nethunter/bleep/docs/scenes.md

# Scenes

## Purpose

A scene coordinates devices and groups through a non-blocking, ordered
sequence. It must remain transport- and brand-independent.

First panel scenario — Press Record (Start):

1. start recording on the Canon camera;
2. wait 500 ms;
3. start recording on the Tascam recorder.

Press Stop (generated by reversing and inverting Start):

1. stop recording on the Tascam recorder;
2. wait 500 ms;
3. stop recording on the Canon camera.

Later example with lights/groups (full Phase 6 gate):

1. turn on the light group;
2. wait one second;
3. start recording on the camera;
4. wait one second;
5. start recording on the Tascam recorder.

The panel and Portal generate a materialized reverse/inverse Stop by default
(ADR-037). The user can copy that preview into a separately authored Custom
Stop, preserving the flexibility introduced by ADR-019. Every target is
prepared concurrently when the sequence run screen opens, with links held
until Back or Unlink (ADR-020). ADR-021 supplies one scanner and independent
async connection slots, so selecting one target does not stop discovery for
the other preparing targets. A physical BLE connection alone is insufficient:
the runner remains `Connecting` until every driver also publishes protocol
readiness after its required discovery, subscriptions, and initialization.
Connection preparation may overlap, but actions and waits execute exactly in
their authored order; the seeded 500 ms wait is editable scene data, not an
engine-level recording delay.

Add Sequence uses a bounded three-stage authoring flow on both panel and Portal:
add and order Start steps, advance to the generated Stop preview, optionally
customize that materialized list, then name and Finish the sequence. The panel
reuses the standard Rename keypad for the final Name. For power-capable lights,
the compound light action applies one stored CCT or RGB look and then powers on
the same fixture without releasing pending state between stages. Its generated
inverse is one Turn Off. Aputure and Zhiyun lights expose this compound action;
Home Assistant lights retain their capability-safe power action.
Existing sequences retain direct Start and Stop editors. Older development
two-step light sequences are unsupported on the selected clean-storage
baseline.

Sequence Settings includes **Duplicate** alongside Rename and the Start/Stop
editors. A duplicated sequence preserves the enabled state, Start steps, Stop
mode, and materialized Stop steps, receives a new stable ID, and opens as
`Old Name (2)`. Names at the 31-character storage limit are shortened before
the suffix so `(2)` remains visible. The Portal suggests the same name while
still allowing it to be changed before duplication. The panel action list
scrolls vertically so Duplicate and Delete remain fully reachable.

Each existing Start or Custom Stop row opens a prefilled step editor. Generated
Stop is read-only until **Customize Stop** copies it into Custom mode. **Use
generated Stop** confirms before discarding the override and relinking Stop to
Start. Wait rows expose a
bounded millisecond duration control, parameterized **Set look** or
**Set look + On** rows
preserve and edit their saved CCT/RGB values, and ordinary action rows reopen the target's
capability-safe action picker. Saving replaces that row in place rather than
appending another step. Back from this existing-step editor returns directly to
the step list; changing target or action is done by adding a replacement step
and reordering it. Taller two-tier rows keep the action label above the
reorder/delete buttons. `Add step` is the final scrollable row rather than fixed
screen chrome, and adding a Wait uses the same duration editor.
New Wait steps default to 200 ms; existing saved waits retain their authored
duration.

Editing a prepared scene reconciles its target set in place. Links for targets
that remain in the materialized Start/Stop lists stay held, removed targets are
released, and newly added targets prepare before the scene returns to `Ready`.
Completing Stop keeps prepared links while the run/edit screen remains open so
the sequence can be edited or restarted without reconnecting. Back and Unlink
perform teardown.

Deleting a sequence while it is only preparing connections first cancels that
preparation and releases its links, then removes the record. Delete remains
disabled while Start/Stop is executing or the sequence is armed.

The run screen deduplicates direct targets across both authored lists and shows
each as a circular category-icon chip. The border communicates live readiness:
breathing cyan while connecting or initializing, green when protocol-ready,
red after a terminal connection failure, and muted gray when simply
disconnected or powered off. Retry backoff remains part of Connecting and keeps
breathing cyan. Tapping a chip outside Start/Stop execution opens that target's
full controls using the held activation. Returning preserves all links and the
sequence's logical phase; manual record commands are per-device overrides, so a
later authored Stop still runs for every target. Sequence Start/Stop controls
stay disabled while any stable-phase target is not ready.
The compact run status uses blue for connection/transitions, green for
Ready/Done, red for Recording/failure/disconnection, and muted text for Idle.

A partial Start action failure keeps sequence ownership and exposes Stop.
Generated and Custom Stop still visit every materialized target. Canon Smart and Tascam
treat Stop as a successful no-op when that device already confirms `Stopped`,
so a target that never began recording cannot abort cleanup before another
target is stopped. Unknown or recording targets still receive the protocol Stop
command and require their normal device-originated confirmation. A successful
Stop reaches `Completed`, where Start is enabled for another attempt.

While a sequence run screen is open, a short hardware-button press mirrors the
enabled run action: Start when the sequence is ready (or restartable), and Stop
when it is armed or Start is in flight. It does nothing while preparation or
Stop is already in progress. A long press mirrors the visible Back control:
Settings closes first, the step editor returns to Run, Run returns to the
sequence list and releases sequence ownership, and the list returns Home.

## Data model

A scene contains:

- stable ID, name, enabled state, and schema version;
- ordered Start steps;
- Stop mode: generated inverse or Custom override, plus the materialized Stop
  list used by the current runner;
- default timeout and failure policy;
- optional descriptive notes.

The number of scenes is not a compile-time product limit. The registry grows
on demand. Schema-v4 persistence retains schema v3's compact authored-step
encoding and adds generated/custom Stop mode. Creation is transactional: if RAM
or NVS cannot hold another scene, that attempted scene is not committed and
existing scenes remain intact. The per-scene step bound is retained because the
runner and editor operate on fixed, explicitly validated Start and Stop command
lists.

Step types:

- `Action`: send one typed command to a device or group;
- `Wait`: schedule the next step after a duration;
- `Parallel`: execute a bounded list of child actions together.

An action stores a stable target ID and capability command, not a brand-specific
function name.

Conceptual example:

```json
{
  "id": "studio-record",
  "name": "Studio Record",
  "stopMode": "generated",
  "start": [
    {
      "type": "action",
      "target": "group:lights",
      "command": "light.power_on"
    },
    {
      "type": "wait",
      "milliseconds": 1000
    },
    {
      "type": "action",
      "target": "device:main-camera",
      "command": "recorder.start"
    },
    {
      "type": "wait",
      "milliseconds": 1000
    },
    {
      "type": "action",
      "target": "device:tascam",
      "command": "recorder.start"
    }
  ]
}
```

The final schema may use a compact binary representation in firmware, but the
Portal-mode HTTP API should expose a versioned, readable format.

## Authoring-time generation

Generated Stop walks Start backward and maps commands as follows:

- light on ↔ light off;
- recording start ↔ recording stop;
- record trigger, Home Assistant Press, and Activate repeat unchanged;
- absolute CCT/RGB settings are omitted because the previous value is unknown.

A wait reverses to the same duration. Generated Stop is refreshed atomically
after every Start add, edit, reorder, or delete. Custom Stop is independent and
is not modified by later Start edits.

Schema 4 stores the mode and materialized list. Version 0.3.0 accepts only that
current encoding; older development schemas are rejected at load and are not
migrated or erased automatically.

## Execution journal

Success journaling remains later Phase 6 work. The current generated Stop is
authoring-time data and intentionally preserves the existing cleanup rule:
after partial Start failure, Stop attempts every generated target because a
device may have acted without confirming success.

Journal state includes:

- scene and run IDs;
- current step and direction;
- started, completed, failed, skipped, and canceled results;
- per-device group results;
- timestamps and state quality.

Persistence across power loss is a later policy decision. The initial engine
must fail safe and show that the previous run ended unexpectedly.

## Timing and concurrency

`Wait` is scheduled from monotonic time. It must not call `delay()` or block
Bluetooth, HTTP, LVGL, reconnect, or cancellation.

Parallel execution is bounded by configured queue and connection limits.
“Parallel” means dispatched without an intentional ordering delay, not
electrically or transactionally simultaneous.

## Failure policies

Each step may use:

- `abort`: stop Start execution and expose completed actions for rollback;
- `continue`: record failure and proceed;
- `retry`: retry within a bounded count and timeout.

No scene is atomic across independent hardware. UI and HTTP responses must show
per-step and per-device results.

## Validation

Before saving or running, validate:

- target IDs exist and are enabled;
- target drivers are compiled into this firmware;
- device or group exposes the command capability;
- generated Stop follows the ADR-037 command mapping;
- waits, retries, and timeouts are within configured limits;
- queue and nesting limits are respected;
- movement actions satisfy additional safety rules.

## Portal-mode HTTP editing

The temporary Portal-mode access point provides:

- scene list, create, duplicate, rename, enable/disable, and delete;
- ordered drag/reorder editing;
- device/group target picker filtered by capability;
- action parameters and wait duration;
- generated Stop preview;
- optional explicit Stop editor;
- validation results;
- import/export and a dry-run validation endpoint.

Editing APIs exist only while Portal mode is active. Exiting Portal mode or
reaching its inactivity timeout stops the HTTP server and access point.
