nethunter/bleep/docs/decisions.md

# Architecture Decisions

This log records accepted decisions. Add a new numbered entry when a choice
changes architecture, compatibility, persistence, safety, or user workflow.
Do not silently rewrite an accepted decision; mark it superseded and reference
the replacement.

## ADR-001: Direct on-device control

- Status: Accepted
- Decision: Device integrations and scene execution run on the ESP32-C3 remote,
  not on an external gateway.
- Consequence: Bluetooth Mesh, GATT, Wi-Fi, HTTP, LVGL, and scene scheduling
  must coexist within a constrained memory budget.

## ADR-002: Compile-time driver selection

- Status: Accepted
- Decision: Use ESP-IDF Kconfig/menuconfig to choose device families, model
  drivers, transports, and optional subsystems.
- Consequence: Disabled drivers must be removed from the binary. Runtime
  enable/disable controls behavior but does not reclaim linked memory.

## ADR-003: Drivers and instances are separate

- Status: Accepted
- Decision: Compiled drivers describe supported models; persistent runtime
  instances contain pairing, endpoint, name, enabled state, and group data.
- Consequence: One driver can support multiple physical devices, and dormant
  instance records survive a build that omits their driver.

## ADR-004: Unified capability UI

- Status: Accepted
- Decision: Reuse UI modules by device type and capability rather than by
  brand. Drivers may add specialized extensions where necessary.
- Consequence: Lights, cameras, motion devices, and recorders receive
  consistent controls while Shark retains its specialized keypoint workflow.

## ADR-005: Amaran onboarding supports two paths

- Status: Accepted
- Decision: Support both panel-owned provisioning of factory-reset lights and
  import of an existing Sidus/amaran mesh.
- Consequence: The first release uses one active studio mesh and treats mesh
  keys as secrets.

## ADR-006: Canon supports Bluetooth and HTTP

- Status: Accepted
- Decision: Canon EOS R6 family drivers support BR-E1-compatible Bluetooth and
  CCAPI HTTP independently, including HTTP with Bluetooth fallback.
- Consequence: HTTP can provide confirmed recording state; Bluetooth-only state
  is optimistic unless later protocol research finds reliable readback.

## ADR-007: Groups are capability-safe

- Status: Accepted
- Decision: A group exposes only capabilities shared by all enabled members.
- Consequence: Commands and scene steps cannot silently target unsupported
  members.

## ADR-008: Scenes are ordered and reversible

- Status: Accepted
- Decision: Scenes contain ordered actions, waits, and optional parallel
  groups. Stop is generated by reversing/inverting successful Start actions by
  default, with an explicit Stop override available.
- Consequence: Commands declare safe inverses and execution uses a per-action
  journal.

## ADR-009: Administration is USB-only

- Status: Superseded by ADR-011
- Decision: Serve the HTTP administration portal on PPP or SLIP over USB
  serial, never on Wi-Fi.
- Consequence: Wi-Fi remains available for outbound Canon CCAPI, while portal
  availability depends on the USB network link. Host setup and upload/logging
  coexistence require an early feasibility spike.

## ADR-010: Main-loop ownership

- Status: Accepted
- Decision: All parsing, state mutation, commands, scene transitions, and LVGL
  access occur from `loop()`. Transport callbacks only queue bytes or events.
- Consequence: New transports must be bounded and non-blocking.

## ADR-011: Administration uses a dedicated temporary AP mode

- Status: Accepted
- Decision: The administration HTTP server runs only in an explicit Portal
  mode on a temporary open SoftAP or its bounded station handoff.
- Consequence: Entering Portal mode suspends scenes, device links, and studio
  Wi-Fi. Exit, inactivity timeout, or reboot destroys the HTTP server and AP.
  No administration listener consumes resources during normal operation.

## ADR-012: Boot always opens Home

- Status: Accepted
- Decision: Startup displays a neutral Home menu and does not automatically
  scan, pair, re-pair, reconnect Shark, or load a device screen.
- Consequence: Opening a device screen or launching a scene explicitly requests
  the required connections. Devices, Groups, Scenes, Portal, and power/status
  are available from Home.

## ADR-013: Advance the multi-device foundation before feasibility spikes

- Status: Accepted
- Decision: Implement the bounded driver catalog, device manager, persistent
  runtime registry, Home/Devices UI, and on-demand Shark lifecycle before the
  Phase 1 coexistence and Portal spikes. The first build compiles only the Shark
  driver and permits one Shark instance, while retaining up to eight dormant or
  future device records.
- Consequence: This is an explicit roadmap deviation that advances selected
  Phase 2, Phase 3, and Phase 7 work while the Phase 0 physical behavior gate
  and Phase 1 feasibility gates remain open. No Amaran, Canon, group, scene, or
  Portal support is implied by the framework.
- Persistence: Registry schema version 1 is stored as a checked NVS blob in the
  `studio` namespace. Existing `shark` pairing keys migrate into the initial
  record and remain available for rollback until hardware verification passes.
- Lifecycle: Boot loads configuration and Home without initializing NimBLE.
  Opening the enabled Shark record activates scan/connect/reconnect; leaving its
  screens stops motion, scanning, retries, and the connection.

## ADR-014: Canon BLE exposes an honest record trigger

- Status: Accepted
- Decision: Advance a bounded Canon BR-E1 BLE tranche for EOS R6 Mark III
  hardware research before the full Phase 1 coexistence gate. The BLE
  capability is a stateless record trigger, not separate record-start and
  record-stop commands.
- Consequence: The panel does not infer or display recording state from BLE.
  BR-E1 sends the same movie trigger for both transitions and provides no
  equivalent state readback. Distinct start/stop commands and confirmed state
  remain CCAPI work. The tranche may use the existing one-active-instance
  manager and does not prove concurrent Shark/Canon links or complete Phase 1.
- Protocol status: Pairing, bonded reconnect, and the movie-mode `0x88`/`0x08`
  press/release sequence from public reverse-engineering are functionally
  verified on the EOS R6 Mark III. Captures and extended stability measurements
  remain `Research`.

## ADR-015: Canon exposes Trigger and Smart drivers

- Status: Accepted
- Decision: Present the two Canon workflows as separate compiled drivers and
  device choices: `Canon (Trigger)` for BR-E1-compatible BLE, and
  `Canon (Smart)` for smartphone-mode BLE handoff followed by direct Wi-Fi
  CCAPI.
- Consequence: Trigger remains the fast stateless fallback. Smart owns
  smartphone-mode pairing, requests the camera Wi-Fi access point, obtains the
  handoff connection data, joins that network, and uses CCAPI for distinct
  record start/stop and confirmed state. A Smart failure may fall back to a
  separately configured Trigger instance only when the user selects that
  policy.
- Research status: Sanitized EOS R6 Mark III host-HCI fixtures identify the
  Camera Connect request that starts Wi-Fi, its response indications, and the
  SSID-like and credential-like characteristics. `Canon (Smart)` remains
  blocked until network-side capture identifies security mode, DHCP behavior,
  the camera HTTP endpoint, and the first successful CCAPI request. Do not infer
  those missing details from successful BLE handoff alone.

## ADR-016: Tascam X8 record-control tranche

- Status: Accepted
- Decision: Advance the Tascam Portacapture X8 from the future recorder list as
  a bounded AK-BT1 BLE tranche with connect, explicit record start, explicit
  record stop, and recorder-confirmed recording state.
- Evidence: The annotated nRF52840 research capture summarized in
  `docs/protocols/tascam-x8.md` confirms the custom GATT service, COBS stream
  envelope, session keepalive, start/stop commands, and state events for both
  app-originated and recorder-originated actions. Golden vectors and confidence
  labels are recorded in `docs/protocols/tascam-x8.md`.
- Consequence: Tascam gets typed `RecordStart` and `RecordStop` commands rather
  than reusing Canon Trigger's stateless toggle. The UI may show recording only
  after the recorder's confirmed `DR 20 20 24 01` start event and stopped only
  after `DR 10 20 08`; ATT write responses are not physical success. No stable
  recording boolean was confirmed in the original fixture. A subsequent
  controlled reconnect capture confirms `DR 20 20 00` values `0x81` recording,
  `0x10` stopped, and transitional `0x82`. Battery, media status, mixer control,
  and other Portacapture functions remain future research.
- Roadmap deviation: This tranche advances a future recorder driver while the
  Phase 0/foundation and Canon verification gates remain open. It does not
  begin dependent scene or group work and retains one active transport.

## ADR-017: Canon smartphone BLE ships beside Trigger

- Status: Experimental
- Decision: Compile both ADR-015 Canon choices. `Canon (Trigger)`
  (`DriverId::CanonTrigger = 4`) keeps the verified BR-E1 remote service
  (`00050000-...`, movie-mode `0x88`/`0x08`). `Canon (Smart)`
  (`DriverId::CanonBle = 2`) keeps the Camera Connect smartphone-mode BLE
  pairing and shooting services as a BLE-only experiment until CCAPI handoff
  evidence lands. Both may be present in one firmware build; the operator
  picks the matching camera menu (Remote vs Connect to smartphone). Only one
  transport remains active at a time.
- Evidence: Public EOS M6 Camera Connect reverse-engineering documents the
  `00010000-...` handshake service and `00030000-...` shooting service. The
  minimized EOS R6 Mark III host-HCI research findings summarized in
  `docs/protocols/canon-smartphone-ble.md` confirm confirmation-first pairing,
  explicit movie start/stop writes,
  shooting-state notifications, and the `00020002-...` Wi-Fi handoff request
  with `00020003-...` responses. The handoff fixture excludes serial,
  controller, SSID-like, credential-like, and SMP key material. BR-E1 Trigger
  remains hardware-verified on EOS R6 Mark II/III.
- Consequence: Smart exposes explicit `RecordStart`, `RecordStop`, and
  recording-state capability, but reports state as unknown until a
  camera-originated `00030031-...` notification is observed. ATT write success
  is not recording confirmation. Trigger stays stateless (`RecordTrigger` only).
  Existing BR-E1 bonds and Smartphone bonds are not interchangeable; forget and
  re-pair when switching modes or bodies.
- Relationship to ADR-015: Smart remains a bounded BLE-only experiment, not the
  production BLE-to-Wi-Fi CCAPI workflow. It does not start a camera access
  point, join Wi-Fi, or implement CCAPI.
- Research boundary: Camera Connect's BLE handoff is captured, but the camera
  network's DHCP/endpoint details and first successful CCAPI request are not.
  Full `Canon (Smart)` Wi-Fi/CCAPI remains blocked on that network-side evidence.
- Roadmap deviation: This experiment advances smartphone-mode pairing and
  BLE-only record control while the Phase 0/foundation and Canon Smart handoff
  gates remain open. It retains one active transport and does not begin scene
  or group work.

## ADR-018: Canon BLE power is explicit and non-destructive

- Status: Experimental
- Decision: Opening the Canon smartphone screen automatically sends captured
  wake mode `03` after setup. Camera power-down is available only through an
  explicit on-screen power control using mode `05`. After confirmed power-down,
  the same control reconnects and runs the captured wake sequence. Reacquiring
  the retained powered-off session from a device screen or sequence also starts
  that reconnect-and-wake attempt; Back only releases the panel's BLE
  connection.
- Safety: Power-down is unavailable while recording is camera-confirmed or a
  record command is pending. Result `01` is only protocol acknowledgement; the
  expected camera-side disconnect is required before the panel reports
  `Powered off`.
- Evidence: The sanitized host-HCI handoff fixture contains repeated
  `03`/`05` wake sequences and `05`/`01` power-down followed by camera-side
  disconnects approximately 147-154 ms later.
- Consequence: A failed or missing power-down disconnect leaves the session
  connected and reports failure instead of assuming physical success. The
  workflow remains hardware-unverified until the ADR-017 gate is exercised.

## ADR-019: Scenes use authored Start and Stop sequences

- Status: Superseded by ADR-037
- Decision: The first on-device scene tranche stores and runs separate ordered
  Start and Stop step lists. Generated reverse-Stop from ADR-008 remains a
  later option, not the default for panel-authored sequences.
- Consequence: Press Record and Press Stop may differ in order, waits, and
  targets. Validation requires at least one non-empty list and capability-safe
  action targets. No inverse journal is required for Stop generation in this
  tranche; per-step progress is still tracked for the UI. Authored Stop remains
  available after a partial Start failure. A Stop action against a target that
  already confirms `Stopped` succeeds as an idempotent no-op, allowing cleanup
  to reach later targets and a completed Stop to make Start retryable.
- First scenario: Start sends Canon `RecordStart`, waits 500 ms, then Tascam
  `RecordStart`. Stop sends Canon `RecordStop`, then Tascam `RecordStop`.

## ADR-020: Sequence runs hold concurrent device links

- Status: Accepted (amended 2026-08-04, 2026-08-09, and 2026-09-03)
- Decision: Opening a sequence run screen prepares every distinct Start/Stop
  target concurrently (`Connecting` → `Ready`). `Ready` requires both a
  physical link and driver-confirmed protocol readiness after required
  discovery/subscriptions/initialization. Links stay held while the run
  screen is open, during Start/Stop execution, while armed after Start, and
  after a successful Stop for immediate restart. Opening Settings, leaving the
  run screen (Back/hide), or selecting Done releases sequence ownership and
  cancels pending preparation so configuration remains editable. Manual
  device screens retain exclusive single-active activation outside sequence
  holds. A sequence target chip may temporarily open that target's full device
  screen by borrowing its held activation; Back returns to the sequence without
  releasing any held target.
- Transition ownership: Switching directly between sequences transfers the
  intersection of their target sets without an ownerless gap. A target shared
  by both sequences, and any physical transport group backing that target,
  remains protected from eviction. Old-only targets are released first and
  become the preferred safe reclamation candidates before new-only targets are
  acquired. This applies equally to retained HA/Wi-Fi and BLE transports.
- Consequence: `DeviceManager` supports a bounded multi-active set across
  different compiled drivers (Canon Smart + Tascam in the first tranche). Start
  from `Ready` does not re-activate targets. Prepare/connect failures surface
  on the run screen. Device screens opened outside the sequence remain blocked
  while it holds links. Sequence-owned target controls are disabled during
  Start/Stop execution, and Start/Stop remain unavailable while any target is
  not protocol-ready. A physical target that reports `pairingRejected` (the
  peer accepts the link and terminates it before bonding, repeatedly) fails
  preparation immediately with `Re-pair <device>` rather than consuming the
  connect budget; the operator must re-pair before the sequence can run. Physical targets are acquired recorders first, then lights, then
  cameras (2026-09-04): the shared central runs one connect at a time, a
  recorder establishes in under a second when awake, and a sleeping camera
  holds the procedure through several failed pokes. Step execution keeps the
  authored order.
  Settings never cancels an active Start, armed recording,
  Stop, or action failure that still permits authored Stop cleanup. A short
  hardware-button press invokes the enabled
  Start/Stop action; a long press follows the same Back path as touch and never
  dispatches Start or Stop. Shark motion remains outside sequences.
- Roadmap deviation: This advances a bounded Phase 6/7 panel-scene tranche
  ahead of groups, Portal HTTP editing, lights, and generated reverse-Stop.

## ADR-021: One shared BLE central owns transport mechanics

- Status: Accepted
- Decision: One lazily initialized BLE central runtime owns NimBLE
  initialization, the physical scanner, bounded client slots, asynchronous
  connect/disconnect callback routing, reconnect timing, address claims,
  controller bond operations, and teardown. Device clients keep advertisement
  acceptance, pairing policy, GATT discovery/subscription, protocol
  handshakes, commands, and notification parsing.
- Threading: NimBLE callbacks copy fixed-size scan, link, and security events
  into a bounded queue. The central and device clients consume those events
  from the Arduino main loop; callbacks do not mutate device state, perform
  GATT writes, or access LVGL.
- Lifetime: Home boot remains BLE-free. The runtime initializes on the first
  acquired link and shuts down after the last owner releases it. Because
  NimBLE client deletion completes asynchronously, shutdown continues pumping
  teardown until the global client slots are actually free. An immediate
  reacquire may reserve logical links while those clients retire; replacement
  clients are provisioned without failing scene activation, and callbacks from
  retired client pointers are ignored. `DeviceRecord` remains the persistent
  identity source; controller bonds are transport state, not a second pairing
  registry.
- Consequence: Concurrent sequence preparation shares one scanner and separate
  async connection slots. Physical connection initiation and security
  procedures are controller-serialized after hardware produced repeated HCI
  `0x3e` establishment timeouts under simultaneous attempts. Discovery remains
  shared, and a queued target may connect while an established target performs
  protocol initialization. Protocol-specific candidate dwell, ignored-peer,
  and direct-versus-scan policy remains in each client. Clients may also cap
  the growing direct-retry backoff (`ConnectPolicy::retryBackoffCapMs`) when
  their peripheral's post-failure silence is a fixed interval; Canon Smart
  uses 1.5 s. `connectPriority` orders queued connects (recorders ahead of
  cameras), `directAttemptsBeforeScan = 0` selects listen-first for peers
  whose blind poke is costly, advertisements carry a `connectable` flag and
  non-connectable ones never start a connect, and the shared scan runs
  without duty-cycle pauses for 15 s while a saved peer that just failed to
  establish is sought (measured AK-BT1 silence after a failed poke: 6-30 s).
- Measurement boundary (2026-08-04): targeted discovery, next-loop setup,
  readiness telemetry, and best-effort connection parameters are implemented
  without changing ownership. A shared asynchronous GATT executor is deferred
  unless hardware timing shows blocking GATT work is at least 25% of median
  readiness for a driver or the Canon Smart + Tascam sequence pair. If that
  gate triggers, amend this ADR before moving generic GATT mechanics into the
  shared layer; drivers retain UUID profiles and protocol semantics.

## ADR-022: Protocol-ready device links persist in a bounded pool

- Status: Accepted
- Decision: `DeviceManager` keeps up to `CONFIG_MAX_ACTIVE_INSTANCES` logical
  sessions active after their screen or sequence owner leaves and maps them
  onto at most `CONFIG_MAX_ACTIVE_LINKS` physical BLE transport groups. A
  driver's `BleSlotKey` is per-instance by default, empty for a non-BLE runtime,
  or shared by logical instances that demonstrably use one real connection.
  Boot remains BLE-free, and an attempt that has never reached protocol
  readiness is canceled when its last owner leaves.
- Ownership: Foreground device screens and sequences hold independent owners.
  Reopening or preparing an already-active instance reuses its session. Leaving
  removes only that owner; retained sessions continue bounded reconnect after
  an unexpected drop. Canon's explicit power-down remains intentional and does
  not trigger reconnect until requested.
- Capacity and safety: When four distinct BLE keys are active, acquisition of
  a fifth key evicts the least-recently-used retained transport group only when
  every logical member has no owner, pending command, or confirmed recording.
  All members are deactivated together so the shared central link is actually
  released. Acquiring another member of an existing group consumes no new
  physical slot. If no group is safe, acquisition fails. Confirmed-recording
  links require explicit confirmation before manual Disconnect. Disconnect,
  disable, forget, remove, Portal entry, and controller shutdown release the
  session without treating an ACK as proof of device state.
- Scene handoff: changing scenes transfers ownership for targets in the set
  intersection and releases ownership for old-only targets. Release does not
  disconnect protocol-ready sessions. No scene-specific cleanup bypasses the
  pool: ownerless Canon, Tascam, HA, and light sessions remain retained while
  logical and BLE capacity permit, and only a subsequent capacity-driven LRU
  acquisition may evict them.
- Supersedes: This replaces ADR-013's leave-screen teardown, ADR-018's statement
  that Back releases the Canon link, and ADR-020's leave-sequence teardown and
  manual single-active restriction. Their boot, power safety, sequence
  readiness, and borrowed-control decisions remain accepted.
- Consequence: The shared BLE runtime remains initialized while any retained
  transport group owns a central slot. Under ADR-030 the panel-owned
  Amaran/Aputure/Zhiyun mesh has one shared key; Home Assistant has none.
  Static per-driver session storage must remain within measured ESP32-C3 RAM.

## ADR-023: Bounded local Home Assistant entity client

- Status: Experimental; amended 2026-08-04; hardware feasibility gate open
- Decision: Add one shared Home Assistant client for at most four selected
  `light`, `switch`, `input_boolean`, `button`, `scene`, and `script` entities.
  V1 is client-only: Ble(e)p does not expose its physical devices to Home
  Assistant. Lights are power-only. Local plaintext `http://` and `ws://`
  endpoints plus a pasted long-lived access token are allowed; TLS, cloud
  access, OAuth, devices/areas, and other domains remain deferred.
- Provisioning boundary: First-time Portal setup performs a bounded nearby-network
  scan before creating an open SoftAP. The AP console administers local device
  records and sequences without studio Wi-Fi and may collect studio Wi-Fi
  credentials for Home Assistant. The initial scan is cached, but an explicit
  browser request starts a fresh non-blocking scan while preserving AP HTTP/DNS
  service. The panel exposes the setup AP as a standard
  open-network Wi-Fi QR code. Wildcard DNS and HTTP redirects trigger the phone's
  captive-network sign-on UI on a best-effort basis while that AP is active;
  both are destroyed before LAN Portal startup. Manual SSID entry remains
  available for hidden networks. During the non-blocking join it uses AP+STA while the listener
  remains bound to SoftAP and both the browser and panel report progress or a
  bounded failure reason.
  After a successful join, it destroys the AP listener and AP, then binds a new
  listener to the station address. The assigned numeric address is authoritative
  and shown during handoff; `http://bleep.local` is a best-effort mDNS alias.
  The LAN Portal enables Home Assistant URL/token/entity setup and is reachable
  only while Portal remains open on the panel. Entering Portal cancels scenes
  and physical links; explicit Exit or ten minutes of inactivity destroys the
  listener and disconnects Wi-Fi. Normal Home boot remains network-free.
- Persistence and capacity: Device schema v2 adds a tagged HA domain and
  canonical entity ID while decoding v1 BLE records unchanged. Wi-Fi password
  and HA token live in a separate checksummed NVS record and are excluded from
  ordinary device backup/UI responses. The registry grows from eight to twelve
  records: eight physical records plus four HA entities. Active runtime-instance
  capacity is separate from the four-link BLE transport limit because HA
  instances share one network session.
- Runtime: Use Home Assistant's documented bearer-token REST API and
  authenticated `/api/websocket` API only. Resolve initial states individually,
  subscribe only to active entities with `subscribe_trigger`, and rebuild that
  subscription as ownership changes. WebSocket callbacks enqueue bounded raw
  frames; JSON parsing, state mutation, service calls, and LVGL access stay in
  `loop()`. A successful authenticated subscription is command-ready even when
  heap pressure defers initial REST state confirmation; that entity remains
  explicitly unknown until REST or an event confirms it. A successful service
  result completes both stateful and stateless actions because an idempotent
  call may produce no state-change event; API acceptance does not upgrade the
  entity's independently reported state quality.
- Safety and scenes: Generic `TurnOn`, `TurnOff`, `Press`, and `Activate`
  commands are capability-checked through each instance's dynamic profile.
  Lights and switches expose explicit On/Off controls. Input booleans retain
  explicit On/Off commands for safe scene authoring but present one
  context-sensitive action button on their entity screen. HA scenes/scripts
  expose only Activate. No Toggle or value action is inferred.
  Portal refuses to remove an entity referenced by a Ble(e)p scene and may
  rebind an existing instance ID so those references survive entity-ID changes.
- Feasibility gate: Before this moves beyond Experimental, verify on the target
  board AP-to-LAN handoff, LAN listener lifetime, REST discovery, authenticated WebSocket subscription,
  LVGL responsiveness, teardown, and heap recovery across ten Portal and ten
  runtime connect/disconnect cycles. Stop promotion and document the limiting
  resource if any gate fails. The uncommitted multi-instance `DeviceManager`
  work present when this tranche began is the authorized implementation
  baseline and must be preserved.
- Hardware constraint observed 2026-08-04: Opening an authored HA-first mixed
  sequence started Wi-Fi before the lazy BLE central. NimBLE then failed its
  contiguous `0x7800` allocation (`BLE_INIT: Malloc failed`) and asserted into
  an interrupt-watchdog reset. Preparation now acquires all physical targets
  before HA targets regardless of authored action order. Amendment
  2026-09-03: the ordering protects NimBLE's initialization allocation, not
  peripheral wake time, so the platform may supply an early-network policy
  (`SceneRunner::setEarlyNetworkPolicy`). `main.cpp` permits HA Wi-Fi once
  the BLE central holds a link and free heap is at least 56 KB with a 40 KB
  largest block; otherwise HA still waits for every physical target. An
  early-started HA keeps the full network connect budget measured from the
  later of its own start and the moment the physical targets became ready.
  Station joins reuse the last successful channel/BSSID within a boot
  (`wifi_station_cache`), and the HA runtime turns the radio off through a
  settled main-loop shutdown instead of an immediate `WIFI_OFF`. A subsequent live
  run proved that two BLE sessions left too little heap for the Wi-Fi driver's
  four required RX buffers. At that tranche the target used two 20-row DMA display strips,
  a 76 KiB LVGL pool, and two 2 KiB HA frame slots. The complete simulator flow
  passes at those bounds; a measured 72 KiB LVGL pool was rejected. WebSocket
  disconnects now reset protocol state and schedule a main-loop reconnect
  instead of leaving the runtime permanently unauthenticated. These
  mitigations have native/simulator coverage, and one mixed
  HA/Canon/Tascam hardware run reached all-targets-ready in 8.6 seconds. The
  ten-cycle teardown/heap-recovery gate remains open. Later UI lifetime work
  reduced the display strips to 15 rows, and ADR-035 now validates a 64 KiB
  LVGL pool without changing those strips.

## ADR-024: Userspace PB-GATT and Mesh Proxy for the first Amaran tranche

- Status: Experimental; target-light hardware gate open
- Naming: Superseded by ADR-038. The picker, driver, build profile, and shared
  runtime now use the canonical `Aputure Light` identity.
- Decision: the picker exposes one generic `Aputure Light`. The first nearby
  factory-reset fixture advertising Mesh Provisioning is added; Pano 60c,
  Pano 120c, and Ace 25c are validation targets rather than separate user
  choices. Compatible fixtures use Bluetooth Mesh PB-GATT for no-OOB
  provisioning and Mesh Proxy GATT for control. Ble(e)p creates one
  panel-owned mesh and does not depend on ESP-IDF's mesh host, Sidus Link,
  Home Assistant, or Python at runtime. Existing-mesh import remains deferred.
- Runtime: One panel-owned mesh consumes one physical `DeviceManager` link slot,
  regardless of its logical fixture count. One selected member supplies the
  proxy bearer, with other proxy-capable members available for fallback. The
  runtime uses the same lazy NimBLE central as the existing GATT drivers.
  Host-task callbacks only enqueue bounded raw notifications; all provisioning,
  cryptography, persistence, configuration, writes, state mutation, and LVGL
  work stays in `loop()`.
  This is now enforced by a shared Amaran-family `BleSlotKey`; native coverage
  fills all four physical slots, activates a second logical mesh member without
  eviction, and verifies that LRU eviction releases the complete idle mesh
  group rather than one member.
- Persistence and replay safety: A separate checksummed NVS record contains the
  mesh identity, keys, IV index, addresses, node device keys, and configuration
  phase. Sequence numbers are durably reserved in blocks of 256 and commands
  stop before the 24-bit space can be reused. A provisioned node is persisted
  as pending configuration before the provisioning link is released.
- Commands and state: Parse Composition Data before selecting models; Ace 25c
  (`0x0211:0x0000`) and MC Pro (`0x03F6:0x1000`) are not interchangeable.
  Generic OnOff transactions are confirmed on both; Light Lightness
  transactions are confirmed on Ace. Generic OnOff is a writable shadow on
  both tested fixtures: operator-watched Off changed each model while neither
  emitter changed. Use it only for reachability, never emitter power/control.
  Subscribe useful standard models and the composition-selected vendor model
  to the panel-owned group so one refresh/action may receive individually
  sourced statuses. The group-addressed Telink `0x26` power Set physically
  controls the tested Ace 25c and MC Pro, and its `0x0E` group poll returns
  independently sourced, physically correlated power status. The identical
  power Set sent unicast had no effect. Track proxy-bearer state separately
  from per-node reachability,
  confirmed model present/target state, transition deadline, last authenticated
  response, and separately qualified emitter state. Use only the confirmed
  group power subset for this fixture pair; other captured Telink `0x26`
  writes remain optimistic and are not a generic Amaran/Aputure control path.
  The runtime now decrypts and authenticates complete unsegmented Proxy Network
  PDUs, rejects non-AppKey traffic and replayed per-source sequence numbers,
  polls vendor power at five-second intervals, and expires a member after a
  fifteen-second response gap. This confirms emitter power and reachability
  without interpreting a missing response as Off. ADR-030 enables the now
  hardware-verified group power writes and deterministic per-member RGB-group
  writes. CCT/tint readback,
  HSIC, interpolation, and vendor-property readback remain deferred.
- Safety gate: AppKey/model/subscription configuration uses segmented lower
  transport where required and advances only after decoded success status.
  Promotion still requires the remaining initial validation fixtures,
  interrupted configuration, reboot recovery, sequence-number continuity, and
  verified node reset. Ace/MC cross-routing, bidirectional proxy selection,
  acknowledged standard-model state, a 20/20 alternating-node response soak,
  and group physical power Set/Get are now radio- and operator-evidenced. Other
  physical output properties remain an operator-assisted gate. Until verified
  reset is implemented, ordinary local
  record removal is not a claim that the fixture left the mesh.

## ADR-025: Battery-conscious runtime policy does not replace input protection

- Status: Accepted; target endurance gate open
- Context: Three user-reported CrowPanels stopped running from battery after a
  few days while continuing to work from USB. On one failed board, the battery
  measured about 4.0 V and D1 measured about 4.0 V on one side and 2.4 V on the
  other. This is evidence of a battery-input-path fault, but the exact failed
  component and electrical cause remain a `Hardware hypothesis` until board
  schematics, part identification, current waveforms, and destructive analysis
  are available.
- Decision: Initialize BLE from the compile-time `CONFIG_BLE_TX_POWER_DBM`
  setting, defaulting firmware profiles to +6 dBm; use a 40/100 active scan
  window/interval in four-second bursts with 1.5-second pauses; suspend scanning
  while the controller initiates or secures a connection, then resume it for
  remaining discovery requesters; request 30-50
  ms connection intervals after protocol setup; and enable Wi-Fi station modem
  sleep for the retained Home Assistant session. Healthy protocol-ready sessions remain
  retained across navigation. If an ownerless retained session drops
  unexpectedly, deactivate it instead of running background reconnect. Canon
  Smart's intentional `PoweredOff` state remains retained so acquiring it can
  run the accepted wake path.
- Amendment (2026-08-09): the prior 20/100 duty cycle was raised to 40/100 to
  reduce sparse-advertisement discovery latency. Suspending discovery during
  connection establishment confines the additional scan airtime to periods
  when it cannot compete with the failure-prone initiator/security procedure.
  Battery endurance and cold multi-device readiness remain hardware gates.
- Display: Keep the screen and backlight on continuously. The PI4IOE5V6408
  exposes the backlight as a plain GPIO with no hardware brightness level, and
  the operator prefers immediate input without dimming or wake suppression.
  This does not reintroduce software power-off or deep sleep; the SPDT switch
  remains the only controller power control.
- Safety boundary: Firmware can reduce average draw, radio peaks, and needless
  retry activity. It cannot limit inrush, block reverse current from USB,
  correct an underspecified diode/MOSFET, or guarantee that D1 will survive.
  New boards still require external battery-path protection or replacement
  power hardware before a multi-day endurance result can be treated as safe.
- Assembly amendment (2026-08-11): The reference enclosure build desolders and
  removes the CrowPanel's original D1, then installs an external through-hole
  1N5819 in its place. The original and replacement must not remain connected
  in parallel. The hardware guide owns removal, wiring, polarity, insulation,
  strain-relief, and first-power checks. This standard assembly step does not
  close the endurance gate or establish a universal current or thermal rating
  for manufacturer-variable diode parts.
- Gate: On a protected new board, verify scan/connect latency, command and
  notification reliability, Canon powered-off reacquire, mixed BLE/HA sequence
  concurrency, and battery-path voltage/temperature over at least a seven-day
  powered endurance run. Do not claim the D1 failure is fixed from builds or
  short functional tests.

## ADR-026: Add-device pairing is transactional

- Status: Accepted
- Decision: Selecting a compiled driver from **Add device** immediately opens
  that driver's pairing flow. The candidate instance remains provisional and
  is excluded from registry enumeration, scenes, and the checked NVS device
  blob until the driver has supplied pairing identity, reached protocol-ready
  state, and the updated blob has been written successfully.
- Failure and navigation: A definite pairing error stays in the provisional
  flow with Retry. Back, hardware long-press, activation failure, or explicit
  cancellation deactivates the transport and asks the driver to clear any
  selected peer, controller bond, or provisional mesh-node data. Reboot during
  pairing restores only the previously committed registry.
- Success: A successful commit preserves the provisional instance ID and keeps
  the user on the ready device controls. A failed persistence write remains a
  provisional error with Retry rather than exposing an unsaved device as
  configured. Existing committed records, reconnects, and Portal-managed Home
  Assistant entities retain their prior lifecycle.
- Persistence: The device schema is unchanged. Prepared records are inserted
  into the in-memory registry only at commit, with existing capacity,
  per-driver limits, and monotonic committed instance IDs enforced.

## ADR-027: Portal administration is configuration-only and physically entered

- Status: Accepted
- Scope: The AP- or station-bound Portal is a responsive phone/desktop console for
  committed device records, current authored Start/Stop sequences, and Home
  Assistant provisioning. It exposes overview, device, sequence, and HA views.
- Physical boundary: Portal entry remains a physical action on the panel. The
  Portal has no remote entry route, pairing flow, device controls, or sequence
  execution. Physical-device pairing remains on the panel; HA entities may be
  added through Portal because their provisioning is already network-native.
- Session boundary: A fresh unpredictable mutation nonce is generated at each
  Portal entry and embedded in the served page. State-changing requests require
  that nonce, CORS is not enabled, responses are not cached or frameable, and
  the existing ten-minute inactivity and explicit-exit teardown remain in force.
  This is same-origin request protection, not user authentication or transport
  encryption; use remains limited to a trusted local network.
- Consistency: Portal edits use the same checked registries and scene validation
  as the panel. Mutations are transactional with rollback after failed NVS
  writes, revisions reject stale full-record scene updates, and device deletion
  is blocked while a scene references the instance. Dormant records remain
  visible when their driver is omitted from the active build.
- Runtime: Entering Portal cancels scene preparation/execution and releases
  device ownership before starting Wi-Fi. Configuration changes do not acquire
  physical links, and normal operation resumes only after Portal teardown.

## ADR-028: X100 uses shared panel-owned provisioning and confirmed direct control

- Status: Experimental; panel hardware gate open
- Persistence update: ADR-038 replaces the legacy `amaran_mesh` NVS key and
  hidden compatibility driver IDs with a clean-storage development baseline.
- Decision: expose one `ZHIYUN MOLUS X100` light driver that can select a
  factory-reset fixture advertising Mesh Provisioning `0x1827` or an existing
  fixture advertising Mesh Proxy `0x1828`. Discovery requires both the `pl105`
  product identity (`PL105_` name or company `0x0905`) and the expected mesh
  service. A reset light is provisioned with the same no-OOB PB-GATT engine,
  panel-owned network, durable node store, and unicast allocator as Amaran.
  The existing version-1 `AMSH` NVS schema is preserved behind a neutral shared
  repository. Normal X100 control then uses the separate cleartext `0xFEE9`
  GATT service and does not send encrypted Mesh access messages.
- Session and state: after subscribing, the driver reproduces the captured
  identity, firmware, status, and mode initialization sequence starting at
  sequence 2. Protocol readiness requires a validated `pl105` identity and
  device-originated brightness, CCT, and power replies. Power and CCT/
  brightness writes remain pending until correlated read-after-write replies
  equal the request; a GATT write alone never changes published state.
- Lifecycle: successful initialization commits the normal transactional
  add-device record with the discovered BLE identity. The one-instance driver
  uses the shared lazy central and retained-session policy. Callbacks only
  enqueue bounded bytes; framing, CRC validation, correlation, state mutation,
  command completion, and LVGL remain in `loop()`.
- Provisioning recovery: the node record, Device Key, and advanced unicast
  allocator are persisted before the provisioning link is deliberately closed.
  The driver then rescans by product/service for `0x1828`, initializes `0xFEE9`,
  and commits the normal device registry only after confirmed direct readback.
  Persistence failure restores the in-memory store. If the light accepts
  Provisioning Data but disconnects before Complete or durable save, automatic
  reconciliation remains blocked; reset and retry is the documented recovery.
- Gate: verify add, initial state, power off/on, several brightness/CCT values,
  rejection or clamping at 0/100% and 2700/6500 K, reconnect after reboot,
  retained navigation, scene confirmation, timeout/retry, and coexistence on
  the CrowPanel. Optical output must be observed separately from protocol
  readback.

## ADR-029: One multi-instance Zhiyun Light driver selects captured model profiles

- Status: Experimental; extends ADR-028 without changing persisted driver ID 9.
- Decision: present one discoverable `Zhiyun Light` catalog entry. Repeating
  Add Device may create up to four X100 or X60RGB instances. Each session
  accepts only product-qualified `pl105`/`PL105_` or `plx104`/`X104_`
  advertising, remembers the detected profile through provisioning, and
  validates the same marker in the direct identity response. Existing X100
  records remain compatible because the numeric driver ID is unchanged.
- Reuse boundary: both profiles share PB-GATT, mesh ownership and persistence,
  post-provision discovery, retained direct-client lifecycle, `0xFEE9` transport,
  frame scanner, CRC, initialization state machine, power, brightness, and CCT
  control. A profile supplies the state selector byte and identity markers.
- Gateway boundary: the mixed X100/X60RGB vendor-app capture proves one
  `0xFEE9` gateway can route members in a vendor-configured Zhiyun topology. It
  does not prove that PB-GATT provisioning into the same standards mesh creates
  that proprietary topology. Direct panel-mesh probes returned each physical
  gateway's local state for both selector `00` and `01`; ADR-030's shared
  Zhiyun-client boundary is therefore blocked pending vendor-configuration
  research or a return to one direct connection per fixture.
  A later live test provisioned X60RGB into the same panel-owned standards mesh
  as MC Pro and Ace 25c; one X60RGB BLE connection both returned its own
  `0xFEE9` state and routed authenticated responses from the other brands.
  Therefore the eventual transport group is the panel-owned mesh, not a
  brand-specific Zhiyun group. This strengthens but does not remove the shared
  runtime/selector gate.
- X60RGB extension: selector `01 80` adds captured float32 hue `0x1004` and
  saturation `0x1005`. RGB commands convert packed RGB to HSV, then require
  correlated hue, saturation, and brightness write replies before success.
  Effects and current-mode readback are not inferred.
- Capability caveat: the compile-time catalog advertises the union of supported
  Zhiyun capabilities so RGB authoring is available for X60RGB. An RGB command
  sent to an identified X100 fails rather than becoming optimistic. A future
  per-instance capability model may make that distinction earlier in authoring.
- Gate: add an already provisioned and a reset X60RGB from the panel; verify
  CCT, RGB, brightness, power, reconnect, simultaneous X100/X60 retention,
  scenes, timeout recovery, and observed optical output.

## ADR-030: One panel-owned mesh is one cross-brand transport group

- Status: Partially superseded by hardware evidence. Standard Mesh Proxy
  sharing is verified for Sidus-family access traffic; proprietary multi-member
  Zhiyun `0xFEE9` sharing is not valid for the panel-provisioned topology.
- Naming: ADR-038 calls the Sidus-family logical driver `Aputure Light`; Zhiyun
  remains a separate logical driver on the same transport group.
- Decision: Amaran and Aputure fixtures may share
  `BleSlotKey {PanelOwnedMesh, 1}` for standards Mesh Proxy traffic. The current
  shared Zhiyun implementation remains experimental and must not claim
  per-member control: panel-owned PB-GATT provisioning did not reproduce the
  vendor app's proprietary cross-member routing. PB-GATT onboarding remains a
  temporary exclusive operation.
- Zhiyun initialization: identity, firmware, and status requests do not carry a
  member selector and therefore describe the physical proxy fixture. Shared
  sessions run that required gateway setup sequence but accept either supported
  MOLUS gateway identity, then establish logical-member readiness from the
  selector-addressed state replies. Shared member initialization is serialized
  and each member observes a short post-setup quiet interval because interleaved
  setup traffic dropped a selector-0 reply. Direct onboarding retains the
  stricter model-qualified identity check.
- Routing: Persist routing independently from product identity. Each
  Sidus-family node receives a deterministic vendor-model control group derived
  from its provisioned address. ADR-039 supersedes this ADR's common-group
  physical-power behavior: ordinary fixture commands use only the member's
  control group and `0xC000` is reserved for a future explicit group action.
  Each Zhiyun node receives a persisted ordinal `0xFEE9` member selector.
  Mesh-store schema 2 reads schema 1, assigns existing Zhiyun selectors in
  saved-node order, and preserves keys and sequence high-water state.
- Evidence: In one panel-owned mesh, MC Pro `0x0002` vendor model
  `0x03F6:0x1000` subscribed to `0xC001`, Ace 25c `0x0003` model
  `0x0211:0x0000` subscribed to `0xC002`, and X60RGB occupied `0x0004`.
  Through one proxy, independent 5% vendor writes produced visibly red MC and
  green/cyan-green Ace output; X60RGB selector `0` produced confirmed blue
  output. Common-group power then turned the Sidus pair on and off, X60 power
  used confirmed `0xFEE9` readback, and camera frames verified all three lit
  distinctly and all three dark afterward.
- State: A live proxy is only mesh bearer state. Sidus members are individually
  reachable only after authenticated source-addressed status, and emitter power
  comes only from the physically correlated vendor status. Zhiyun values are
  confirmed only by selector/sequence-correlated `0xFEE9` replies. Missing
  replies expire reachability; they never imply Off.
- Zhiyun confirmation: sequence, command, selector, and value correlation on a
  shared physical link did not identify the intended remote fixture. X60RGB's
  direct link returned its own 50%/Off state for selector 1; X100's direct link
  returned its own 52%/Off state for both selectors 0 and 1. The X60RGB gateway
  also reported selector-1 Off while the X100 physically remained On at 52%.
  Until proprietary topology setup is decoded, state from one `0xFEE9` link is
  attributable only to that physical gateway.
- Boundaries: persisted ordinal Zhiyun selectors are not a valid routing
  mechanism for independently panel-provisioned fixtures. The immediate safe
  implementation choice is one direct `0xFEE9` connection per Zhiyun fixture,
  which consumes one BLE slot each; retaining one shared connection requires a
  separate reverse-engineering tranche for the vendor topology setup. Amaran
  configuration still needs decoded status-gated composition enforcement.

## ADR-031: Local settings stay radio-free and factory reset erases all NVS

- Status: Accepted.
- Navigation: Home keeps its four mode tiles and adds a round-safe Settings
  cog. Settings and its child screens are allocated only while open; Home and
  Devices remain the only resident application screens.
- Wi-Fi boundary: the panel may display the saved SSID and that the radio is
  off, but credential changes continue through dedicated Portal mode. Opening
  Settings or Wi-Fi status never starts Wi-Fi, a listener, or device links.
- Preferences and support: haptic feedback defaults on and persists in its own
  checked record. About identifies the semantic firmware version, Git commit
  and commit date, hardware profile, and license. System Info exposes only
  sanitized heap, physical-link-count, and radio-state diagnostics.
- Reset: Factory Reset requires a continuous three-second on-screen hold. It
  cancels scenes, tears down radios and device sessions, then erases the full
  NVS partition and reboots without erasing firmware. The warning explicitly
  includes devices, scenes, Wi-Fi/Home Assistant secrets, BLE bonds, haptic
  preferences, and panel-owned mesh keys; provisioned mesh fixtures may need a
  separate manual factory reset before they can be added again.

## ADR-032: New panels start with no default device

- Status: Accepted.
- Decision: A missing device registry is initialized and persisted empty.
  Operators add Shark and every other physical device explicitly through the
  normal transactional Add-device flow.
- Compatibility: If the pre-registry `shark` namespace contains an actually
  paired Shark, it still migrates into the registry. On upgrade, firmware
  removes only the exact untouched placeholder produced by earlier releases:
  an unpaired `Shark Nano II` record with no BLE address or advertised name.
  Paired, renamed, or otherwise identified Shark records are preserved.
- Consequence: Factory Reset returns to an empty Devices list and does not
  silently recreate Shark, while existing owners keep real Shark pairings.

## ADR-033: Each panel owns a stable identity and independent setup domain

- Status: Accepted; identity/setup-AP software implemented, two-panel hardware
  gate open; remaining work is tracked in `docs/multi-bleep-manufacturing.md`.
- Identity: Derive canonical unit ID `BLP-XXXXXXXXXXXX` from all 48 bits of the
  factory eFuse MAC. It survives NVS erasure and is never allocated by a shared
  counter or compiled into a per-unit firmware image.
- Setup AP: Use `Bleep-Setup-XXXXX`, where the suffix is the final five
  hexadecimal characters of the canonical unit ID, and an open initial SoftAP. The QR
  payload declares `nopass`; the panel clearly labels the AP open. Physical
  Portal entry, bounded lifetime, session mutation nonce, and teardown remain,
  but proximity access is an accepted consequence of removing WPA2.
- Mesh: Missing mesh storage creates and immediately persists random Network
  and App Keys. Keys are never derived from the public identity. Separate
  panels therefore own separate mesh security domains even when their mesh
  addresses overlap.
- LAN: Every panel continues to request `bleep.local`. The numeric DHCP address
  displayed beside the canonical unit ID is authoritative when mDNS conflicts.
- Manufacturing: Flash one common image, never clone configured NVS, record the
  eFuse-derived identity against the enclosure, and require a two-panel
  same-room release test.

## ADR-034: Saved, bonded, logical-active, and linked capacity stay separate

- Status: Accepted; four-link hardware coexistence gate open.
- Decision: The full CrowPanel profile stores up to 24 device records, retains
  up to 16 NimBLE bonds, schedules up to eight logical active instances, and
  permits four simultaneous physical BLE transport groups. Build flags now set
  the NimBLE connection pool to four explicitly, and compilation fails if the
  application link limit exceeds it.
- Persistence: Device schema 2 remains unchanged and continues to read older
  blobs. Its larger bounded scratch buffers are heap-backed; save allocates only
  the encoded length. Mesh storage is sized for the same 24-record ceiling.
- UI: Devices shows no pagination controls through six configured records. At
  seven or more, it pages six records at a time. Row trees are released before
  specialized device screens and rename overlays are allocated.
- Boundary: Six links are not a production setting. Raising the physical-link
  limit requires target measurements with the intended mix of encrypted GATT,
  Mesh Proxy, Home Assistant Wi-Fi, navigation, and reconnect activity. The
  ESP32-C3/NimBLE compile-time ceiling is not evidence that those workloads fit
  safely or remain responsive.

## ADR-035: Compiled drivers are flash metadata until an instance is active

- Status: Accepted; mixed-radio hardware gate open.
- Decision: Compiling a driver may add immutable descriptors and executable
  code in flash, but must not reserve per-instance clients, protocol state,
  queues, mesh repositories, sockets, or transport buffers in static RAM.
  Configured instances allocate only persistent registry metadata. A driver's
  full session is allocated with `nothrow` when `DeviceManager` activates that
  instance and is released when the instance is deactivated or safely evicted.
- Shared runtimes: NimBLE, the panel-owned mesh repository/runtime, and Home
  Assistant networking are reference-counted resources. The first active user
  allocates them and the last user releases them. Per-driver maximum instance
  counts are persistence/concurrency limits, not permission to preallocate that
  many sessions. The main loop does not construct NimBLE backend bookkeeping;
  the first BLE activation allocates it, and the final asynchronous client
  teardown frees it. Builds without a BLE-backed driver compile the BLE runtime
  pump out of the main loop.
- Wi-Fi boundary: saved Wi-Fi and Home Assistant configuration never starts the
  radio. Wi-Fi is enabled only while Portal is open or at least one HA entity
  is active, and is disconnected and returned to `WIFI_OFF` after the final
  user. Portal first deactivates device sessions, so it cannot overlap an HA
  runtime accidentally.
- Registry and queues: the 24-record persistence/schema ceiling remains, while
  RAM record storage grows in four-record blocks. BLE control and advertisement
  events use separate bounded queues so bursty advertisements cannot consume
  control-event capacity.
- Memory floor: the target LVGL pool is 64 KiB. Display DMA strip geometry is
  unchanged. The full profile's link-time static RAM must remain documented,
  and mixed BLE plus HA operation must preserve enough contiguous heap for the
  roughly `0x7800` NimBLE initialization allocation.

## ADR-036: Action-camera families stay separate and protocol claims stay narrow

- Status: Experimental; exact-model results exist, while panel and coexistence
  gates remain open.
- Catalog: `GoPro`, `Insta360`, `DJI Osmo`, `Sony Camera`, and `Phone Camera`
  are separate discoverable entries under Cameras. Numeric driver IDs 10-14
  are stable persistence identities and do not alias Canon or one another.
- GoPro: use GoPro's published Open GoPro peripheral service, bonded central
  connection, command/response and query/response characteristics, pairing-state
  command, and Set Shutter on/off. Poll Get Hardware Info until BLE-ready, then
  register Encoding status 10 on every connection. A successful shutter response
  is acceptance only; Start/Stop completes when the camera's Encoding update
  reports the requested state. Mismatched transition state does not complete a
  pending command; bounded Get Status Values polling provides confirmation if
  the notification is missed. GoPro MAX2 desktop-harness and flashed-panel
  cycles confirmed the flow, reported state, and physical Start/Stop. Up to four
  GoPro instances use ordinary per-instance physical slots.
- Phone: act as one lazy BLE HID peripheral named `Ble(e)p Shutter`. Each saved
  phone is identified by its bonded peer identity and consumes one physical
  link; a shutter press sends a bounded Volume Increment press/release to only
  that connection. Bonded reconnect first uses a short directed-advertising
  attempt, then a normal discoverable window because the phone OS remains the
  central and controls whether it reconnects without user interaction. Server
  callbacks only enqueue connection/auth events.
- Insta360: emulate the captured GPS Remote protocol for X5 under the
  operator-confirmed `Insta360 Remote (Bleep)` identity. Its complete name is
  in the primary packet; appearance `0x0180` and proprietary service `0xCE80`
  are in the scan response. The hosted GATT service declares `0xCE82` Notify,
  `0xCE81` Write/Write Without Response, then `0xCE83` Read in capture order.
  The camera initiates the connection, so one shared peripheral
  callback dispatcher separates these peers from Phone Camera. X5 capture
  establishes camera-originated GPS display frames for video idle/elapsed time
  and photo idle/save state; callbacks enqueue raw bytes and main-loop parsing
  is the only source of confirmed recording state. The GPS shutter toggle ends
  in `01 02 00`; Scenes expose distinct Start/Stop operations only when camera
  state makes the toggle idempotent. No raw Shutter action is exposed while
  state is unknown. On a new connection, expose Start immediately from an
  explicitly optimistic video-idle assumption; the first CE81 state replaces
  it. Stop still requires confirmed recording. This accepts the toggle risk if
  the camera was already recording before reconnect. Captured shutdown ends in `01 00 03`;
  wake uses the captured Apple manufacturer `ORBIT` advertisement containing
  the saved camera name's six-character serial for up to 60 seconds. Reconnect
  confirms wake. A Mac CE80-only harness using the same characteristic order
  received unsolicited initial state and completed Start, Stop, and shutdown.
  X5 pairing, state, Start/Stop, shutdown, and physical wake are operator-
  confirmed on the panel. During ORBIT wake, Insta360 owns the returning peer
  even if its unresolved address differs from the saved address, then maps it
  to the single `PoweringOn` session; this reconnect correction remains the
  final hardware recheck. GO Ultra is a
  distinct model and remains an experimental probe;
  current evidence does not establish GPS Remote support.
- Parallelism: synchronization is a core requirement. All compiled
  peripheral-camera services are registered together before the first peer
  connects. Advertising windows may be serialized by the ESP32-C3's one legacy
  advertiser, but established Phone Camera, Insta360, and central-role camera,
  recorder, light, and mesh sessions remain live concurrently within the
  configured physical-link limit. A disconnected target must never tear down a
  ready target merely to advertise.
- DJI: implement DJI's published controller reference for service `0xFFF0`,
  the bidirectional connection handshake, explicit record start/stop, and
  camera-status subscription. Action 5 Pro and Osmo 360 are named candidates
  from that reference; only status pushes produce confirmed recording state.
- Research boundary: Sony's RMT-P1BT GATT behavior is documented by an
  Apache-licensed independent implementation, but panel peripheral-role
  emulation remains unverified. It continues to open `Protocol capture
  required` and cannot commit a device record.
- Gate: verify pairing, bonded reconnect, shutter behavior, cancellation,
  forget/re-pair, four-slot coexistence, and heap return on representative
  GoPro, Insta360, DJI, and iOS/Android/HarmonyOS hardware. Never extend model compatibility
  beyond vendor documentation or observed hardware merely because a product
  listing makes a broader claim.

## ADR-037: Panel-authored scenes generate Stop by default

- Status: Accepted
- Decision: New scenes store `Generated` Stop mode. Editing Start materializes
  Stop by reversing Start and mapping record start/stop and power on/off to
  their inverse. Waits retain their duration. Record trigger, Home Assistant
  Press, and Activate repeat as self-inverting actions; absolute CCT/RGB steps
  are omitted because their prior state is unavailable. **Customize Stop**
  copies the current generated list into an independent editable override, and
  **Use generated Stop** discards that override after confirmation.
- Persistence: Scene schema 4 stores the Stop mode. Main already used schema 3
  for compact variable-count scene storage before this ADR landed, so loading
  schema 1, 2, or 3 converts every scene to Generated, discards its prior
  authored Stop, derives Stop from Start, and rewrites the checked v4 blob. A
  legacy Stop-only scene therefore becomes empty and must be repaired by adding
  Start steps.
- Authoring: Add Sequence is a three-stage flow: author Start, review generated
  Stop with an explicit customization option, then Name using the existing
  Rename UI to finish.
- Execution: Generation is deterministic authoring-time behavior, not the
  deferred ADR-008 success journal. The existing runner executes the
  materialized list and still visits every generated Stop target after a
  partial Start failure, including a target that may have acted without
  confirming success.
- Relationship to ADR-019: Separate authored Start/Stop lists remain available
  through Custom mode, but are no longer the default. Runtime success
  journaling, groups, Parallel, and power-loss recovery remain later Phase 6
  work.

## ADR-038: Aputure Light is the canonical Sidus-family driver identity

- Status: Accepted
- Decision: Present Amaran- and Aputure-branded compatible fixtures through one
  discoverable `Aputure Light` driver. Use `DriverId::AputureLight = 6`,
  `CONFIG_DRIVER_APUTURE_LIGHT`, and the `aputure_light` module, namespace, and
  isolated build profile throughout code, tests, simulator captures, logs, and
  current documentation. Preserve exact product brands in protocol and hardware
  evidence, such as `amaran Ace 25c`, `amaran Pano 60c`, and `Aputure MC Pro`.
- Compatibility: This is an explicitly selected clean-storage `0.2.0-dev`
  baseline. Remove the hidden Pano/Ace compatibility driver IDs and write the
  shared mesh record under the neutral `mesh` NVS key. Operators must run the
  existing on-device Factory Reset before flashing over an earlier development
  build; firmware is not erased by that reset and no automatic erase occurs.
- Shared transport: Zhiyun stays a separate logical driver and retains its
  model-specific commands, confirmed reply semantics, and routing selector.
  ADR-039 moves its panel controls into the shared capability-driven light
  shell. It continues sharing the one panel-owned mesh repository and retained
  proxy client with Aputure Light.

## ADR-039: Light controls and sequence looks are capability-driven and per target

- Status: Experimental; implementation and host gates passed, full fixture
  isolation/coexistence/soak matrix open.
- Routing: Every ordinary Aputure Light On, Off, CCT, tint, brightness, and RGB
  operation targets the fixture's persisted node unicast address. Refresh does
  not transmit until a read-only query is captured. `0xC000` remains
  provisioned for transport compatibility but
  is reserved for a future explicit mesh/group action. Source-addressed status
  updates only the matching logical session. Zhiyun retains its per-member
  selector and selector/sequence-correlated confirmation while sharing the
  same retained proxy connection.
- State and UI: Drivers publish normalized light modes, limits, values, power,
  pending/error state, and confirmation quality through `LightControlState`.
  One shared round-panel shell renders only the supported controls: full
  Aputure CCT/tint/RGB, X100 CCT, X60RGB CCT/RGB, or HA light power only.
- Scenes: append `SetLightCctAndOn` and `SetLightRgbAndOn` without changing the
  scene record layout. Validation requires both Turn On and the selected color
  capability. The panel picker exposes one **Set look + On** action, defaulted
  to 5600 K, 50% brightness, and neutral tint; generated Stop materializes one
  Turn Off. A compound driver transaction remains pending across look and
  power stages and reports any sub-step failure for Stop and Retry recovery.
  The editor previews the currently selected mode and values after a bounded
  debounce while retaining foreground ownership. Aputure compound execution
  sends power first and the requested look last, matching the working Studio
  Lighter transaction and preventing a trailing On packet from restoring CCT.
- Compatibility: the selected clean-storage `0.2.0-dev` baseline does not
  migrate or normalize older two-step light scenes. Factory Reset is the
  documented test baseline.
- Gate: physical output, response attribution, gateway fallback, mixed-device
  operation, reboot cycles, and the two-hour soak must pass per exact fixture
  model before its support claim is promoted.

## ADR-040: Ordinary Aputure controls must never expose mesh-wide power

- Status: Accepted safety correction; independent emitter-power protocol
  remains Blocked.
- Evidence: On the tested Ace 25c and MC Pro, vendor opcode `0x26` changes
  physical emitter power only at common group `0xC000`, where both fixtures
  change together. The same captured command was physically inert at node
  unicast and at each deterministic private group. Generic OnOff is only a
  writable shadow model and does not control either emitter.
- Decision: Aputure device screens and ordinary sequence actions expose only
  independently routed CCT/tint/RGB/brightness looks. They do not advertise
  Turn On, Turn Off, or compound look-and-On commands. The shared shell hides
  power and the scene picker labels the action **Set look**. `0xC000` remains
  read-only for authenticated physical-status polling and reserved for a future
  explicit group action; no ordinary device command writes to it.
- Zhiyun boundary: X100/X60RGB retain confirmed per-selector power and therefore
  keep **Set look + On** with generated Turn Off. Aborting Start cancels the
  exact queued/result request and the driver's pending compound transaction
  before Stop begins, so a late look reply cannot re-arm power-on.
- Recovery: a failed, unconfigured Aputure node may be re-identified as Ace 25c
  or MC Pro after any configuration rejection. Exact device naming follows the
  corrected tuple without overwriting user-authored names.
- Supersession: This ADR supersedes ADR-039 only for Aputure power capability
  and compound actions. The normalized shared shell, per-member look routing,
  and Zhiyun transaction design remain in force.

## ADR-041: Restore captured Aputure per-node power and prohibit command-as-poll

- Status: Experimental correction; host gates passed, four-fixture hardware
  isolation gate open.
- Evidence correction: The working Studio Lighter implementation sends vendor
  power payloads `26 8D ... 01 8C` and `26 8C ... 00 8C` to each light's
  persisted mesh unicast address. Its ordinary state builder selects
  `light.mesh_address` before the network group. Captures likewise show source
  `0x0001` to target `0x0002`. The prior private-group probe did not test this
  production unicast path consistently and therefore cannot establish that
  unicast power is unsupported.
- Decision: Restore Aputure Turn On, Turn Off, and compound **Set look + On**.
  Send every ordinary power and look payload to the selected node's unicast
  address while retaining per-session optimistic/pending state and
  source-correlated replies. Keep the private vendor groups as configuration
  metadata only; reserve `0xC000` for a future explicit user group action.
- Polling safety: Payload `26 0E ... 0E` is a captured group power-on command,
  not a read-only status query. Remove automatic group polling and make Refresh
  a no-write operation until a verified read-only query exists. Proxy/GATT
  connectivity remains bearer evidence, not fixture-state confirmation.
- Identity: The recovery UI offers Ace 25c, Pano 60c, Pano 120c, and MC Pro.
  New nodes first receive Config Composition Data Get. Authenticated,
  device-key-encrypted segmented Composition Data Status selects MC Pro
  `0x03F6:0x1000` or the Ace/Pano `0x0211:0x0000` command model without asking
  the operator. Ace/Pano models share that tuple, so an exact advertised
  product name is persisted separately when available; manual recovery remains
  only for an unsupported or malformed composition response.
- Supersession: This ADR supersedes ADR-040's protocol conclusion and the
  private-group routing sentence in ADR-039. ADR-040 remains the record of the
  safety response to the misleading group experiment.

## ADR-042: Mesh creation and light selection are transactional

- Status: Accepted software boundary; two-panel and physical-selection gates
  remain open.
- Mesh creation: A missing panel-owned mesh is assembled in temporary state.
  An injectable entropy source must successfully fill both the Network Key and
  AppKey, and the complete existing-schema blob must persist, before the live
  repository publishes it. RNG or save failure leaves caller state unchanged.
  Keys are never derived from panel identity, MAC, Portal identity, or setup
  SSID. Existing sequence high-water and node schema semantics are unchanged.
- Selection: A fresh Aputure Light or Zhiyun add scans without claiming a BLE
  peer. The shared round picker exposes at most four compatible advertisements
  with advertised name/model, address suffix, and RSSI. Identity is address
  plus address type and selection uses an opaque stable token. Duplicate
  observations update in place; when full, only a stronger advertisement may
  replace the weakest entry. If exactly one candidate remains through a 750 ms
  discovery-settling window, it is selected automatically without displaying
  a one-row picker. Two or more candidates always require an explicit tap. A
  failed automatic claim exposes the row for manual retry.
- Transaction boundary: PB-GATT connect/provisioning starts only after the
  bounded selection decision. Immediate claim failure rolls back to Scanning.
  A failed
  onboarding/configuration transaction restores the pre-provision mesh node
  set and next unicast address while never decreasing a reserved sequence
  high-water mark. Rollback itself is publish-after-save: if the replacement
  blob cannot persist, the snapshot and pending add remain retryable rather
  than presenting a successful cancel with stale NVS. The normal device record
  still commits only after protocol-ready confirmation. Back/cancel removes
  the draft and provisional mesh allocation.
- Post-provision correlation: Aputure and Zhiyun rediscovery accept the exact
  selected address/type or a standard Mesh Proxy Network ID derived from this
  panel's Network Key. Aputure keeps the provisional transaction across an
  expected post-provision reboot/connect miss and resumes configuration through
  the correlated proxy; a 60-second overall deadline rolls it back. A proxy
  with neither identity nor network proof is ignored. Physical cross-mesh
  rejection remains part of the open hardware gate.
- Compatibility: Saved targets continue automatic reconnect and Aputure and
  Zhiyun retain ADR-041/039 shared-mesh routing. This decision does not alter
  `panel_identity`, `Bleep-Setup-XXXXX`, Portal storage/security, mesh schema
  bytes, or ordinary per-fixture command destinations.
- Gate: native and interactive simulator evidence does not prove physical
  selection, cross-mesh rejection, fallback, or multi-panel coexistence.

## ADR-043: GoPro power control uses wakeable sleep with confirmed transition

- Status: Experimental; published protocol, host/UI implementation, and the
  bounded MAX2 panel Sleep/wake gate are complete.
- Decision: The GoPro screen exposes the same header power affordance used by
  Canon Smart. Power-off sends Open GoPro Sleep command `0x05`, not the legacy
  hard power-down command. It is unavailable while recording is confirmed or
  any record/power transition is pending.
- Confirmation: A successful Sleep command response is acceptance only. The
  session reports **Camera asleep** only after both that response and the
  controller has closed the BLE link and the disconnect is observed. Keeping
  the central connected wakes the GoPro again; missing acceptance or disconnect
  reports failure instead of assuming physical sleep.
- Wake: There is no separate Open GoPro wake command. Pressing power while the
  retained session is asleep first scans the saved peer's documented processor-
  state advertisement. A low-power camera gets a short wake-only connection;
  after its BLE restart, the client waits for an awake advertisement and makes
  a fresh connection for protocol setup. Opening that device or preparing it
  for a sequence invokes the same resume path. Protocol readiness and initial
  Encoding state must complete on that post-boot connection before the camera
  is Ready. A wake attempt is bounded to 30 seconds; failure cancels any queued
  BLE retry and returns to **Camera asleep** so the operator can retry deliberately.
  GoPro documents BLE wake advertising for the first eight hours after sleep,
  so this is not an indefinite remote-power guarantee.
- Consequence: Back does not put the camera to sleep. A sleeping retained
  session remains intentionally offline rather than being evicted as an
  unexpected disconnect. A flashed MAX2 visibly slept, woke, established the
  fresh post-boot control connection, and returned to Ready; other models and
  longer lifecycle/coexistence coverage remain unverified.

## ADR-044: Version 0.3.0 uses explicit ownership boundaries and current schemas only

- Status: Accepted software refactor; target-device behavior gates remain as
  recorded by their protocol ADRs.
- Persistence: Device schema 2, scene schema 4, mesh schema 3, HA schema 1,
  and panel-settings schema 2 are the current encodings. Panel-settings schema
  1 is retained only to migrate the haptics bit while defaulting the new update
  channel to stable, as required by ADR-046. One bounded
  little-endian blob codec owns integer, byte, text, checksum, and bounds
  handling. Golden-byte and deliberate old-schema boundary tests protect it.
  No storage is erased automatically.
- Runtime ownership: `DeviceConfiguration` owns registry persistence and
  transactional mutation; `ActiveInstancePool` owns active slots, connection
  owners, retention, and LRU selection. Scene validation, target leases, and
  action dispatch are separate collaborators while `SceneRunner` remains the
  main-loop phase coordinator.
- Mesh boundary: Mesh records belong to `core/mesh`, not a logical light
  driver. A dynamically allocated `ProxyTransport` reference-counts the logical
  users of the one physical proxy and selects a Zhiyun-qualified bearer when
  any active Zhiyun target requires `0xFEE9`. Aputure and Zhiyun remain separate
  drivers and preserve their command and confirmation semantics.
- UI and composition: Compile-time `DeviceUiHooks` replace central dispatch
  chains, and recorder screens share lifecycle/ownership through
  `RecorderScreenController`. Every driver default is off in the common header;
  full and isolated profiles explicitly opt in. Sony, Insta360, and DJI have
  independent compile flags, and the generic Zhiyun profile name no longer
  encodes X100 as the only model.
- Verification: Host tests, full UI traversal, the Montserrat target build,
  isolated CI profiles, repository-artifact checks, and versioned release
  assets are software gates. They do not promote any open physical behavior,
  coexistence, tactile, reconnect, or endurance claim.

## ADR-045: Firmware updates are signed, dual-slot, and never checked at boot

- Status: Superseded by ADR-046. This records the earlier implemented design.
- Eligibility: Preserve neutral Home boot and `WIFI_OFF`. Automatic checks run
  only after ten continuous idle minutes on Home when due. A successful check
  schedules 24 hours; network failures schedule 1, 6, then 24 hours. Opening
  **Settings > Firmware update** requests an immediate check. Missing Wi-Fi
  offers Portal configuration, while active/retained equipment requires the
  operator to choose **Disconnect & check** or **Later**.
- Consent: Checks fetch only a manifest and detached signature. One modal per
  release sequence offers **Install now** or **Later**. Install requires a
  second confirmation, command idleness, link release, and a USB-power/reboot
  warning. Stable is default; development is explicit opt-in.
- Trust: Canonical bounded manifests are signed with ECDSA P-256. Stable and
  development use different embedded public keys and protected GitHub
  Environment secrets. The target rejects untrusted keys, wrong channel or
  target, malformed/oversized metadata, replayed sequences, non-allowlisted
  payload URLs, bad ESP headers, length mismatches, and SHA-256 mismatches.
- Storage and rollback: NVS remains `0x9000/0x5000`; OTA metadata is
  `0xE000/0x2000`; two application slots are `0x1F0000`; coredump is the final
  64 KiB. CI enforces a `0x1E0000` raw-image ceiling. A new image remains
  pending until approximately ten seconds of healthy main-loop operation, then
  is marked valid. A hold-confirmed Settings action can select the prior
  invalid partition. Existing single-slot panels require the supplied
  no-erase, NVS-preserving USB migration bundle once.
- Publication: successful `main` CI replaces the signed public development
  prerelease. Publishing any non-prerelease GitHub Release triggers stable
  verification/signing without assigning meaning to its tag format.
- Gate: host tests and builds do not prove live HTTPS, Wi-Fi teardown,
  NVS-preserving migration, tamper rejection on target, power-loss rollback,
  stable/development delivery, ten-cycle endurance, or BLE/HA coexistence.

## ADR-046: Firmware updates use fixed recovery and a post-Home startup check

- Status: Accepted software architecture; hardware acceptance remains open.
- Scheduling: Finish stores and render Home before network activity. On every
  configured boot, wait five seconds, then check the selected channel while
  Home remains eligible. Foreground work defers or cancels the check. Preserve
  the ten-minute idle schedule, 24-hour successful cadence, Settings check,
  and 1/6/24-hour network retry sequence. Every updater-owned terminal path
  returns Wi-Fi to `WIFI_OFF`.
- Consent: Background work fetches only the signed manifest and detached
  signature (since 2026-09-04 preferably as the single `bleep-update.bundle`
  asset, falling back to the pair on 404, because each `github.com` TLS
  handshake runs within a few KB of the ESP32-C3 heap floor). A newer, non-dismissed sequence offers **Install now** or
  **Later**. Installation requires a USB/reboot warning and explicit consent
  before scenes and retained links are released.
- Storage: Partition schema 2 contains fixed factory recovery at
  `0x10000/0x100000`, a CRC-protected alternating journal at
  `0x110000/0x10000`, and main `ota_0` at `0x120000/0x2D0000`; NVS and coredump
  remain at their established offsets. Raw ceilings are `0xF0000` recovery and
  `0x2C0000` main. Recovery writes only main; current main alone may replace the
  non-running factory recovery image under ADR-048.
- Trust and health: Both applications embed separate stable/development P-256
  public keys and require manifest partition schema 2 plus recovery schema 1.
  Main persists the exact signed request and applies ADR-048's recovery-first
  ordering. Recovery verifies the request again, streams and hashes main,
  selects `ota_0`, and reboots. Main remains pending until its
  stores, display/touch, Home, and loop survive the ten-second health gate;
  failure returns to factory recovery.
- Factory Reset: A continuous three-second hold enters recovery. Recovery
  downloads and verifies latest stable before erasing NVS. Two alternating
  CRC-protected journal generations make `FactoryResetRequested`,
  `ImageVerifiedResetPending`, and `ResetComplete` resumable and idempotent.
  No networking, signature, image, or hashing failure may erase NVS.
- Gate: Native tests, simulators, packaging checks, and builds are software
  evidence only. USB migration/NVS survival, live cancellation and radio
  teardown, tamper and power-loss boundaries, failed-main fallback,
  stable/development delivery, coexistence, and ten cycles remain hardware
  acceptance gates.

## ADR-047: Wi-Fi credentials can be configured directly in Settings

- Status: Accepted. One-panel visible-network discovery, secured password
  entry, association, DHCP, persistence, and radio teardown are verified;
  retained-link coexistence and repeated-cycle checks remain open.
- Radio ownership: Opening **Settings > Wi-Fi** is read-only and keeps
  `WIFI_OFF`. The panel scans only after **Scan networks** or **Replace
  network** is pressed. A bounded main-loop service owns scan, association,
  DHCP validation, persistence, cancellation, and radio teardown; every
  terminal path returns its radio to `WIFI_OFF`.
- Consent: If retained equipment is active, scanning requires an explicit
  **Disconnect & scan** confirmation. Active commands are never interrupted.
  The panel does not silently release equipment to make room for Wi-Fi.
- Provisioning: The round UI lists at most 16 visible SSIDs, deduplicated and
  ordered by signal strength. Open networks connect directly; secured networks
  use a bounded masked on-screen password editor. Success requires association
  and a non-zero DHCP address, not public-internet reachability. The existing
  Portal remains the fallback for hidden SSIDs, easier phone text entry, and
  Home Assistant configuration.
- Persistence: **Forget network** removes only SSID/password after a warning;
  saved Home Assistant URL, token, and entities remain. Wi-Fi readiness and HA
  readiness are distinct runtime facts, but the HA configuration blob retains
  schema-1 bytes and size so permanently installed schema-2 recovery images can
  continue reading credentials. The stored legacy flag remains the HA flag;
  Wi-Fi readiness is inferred from a non-empty SSID.
- Gate: Panel `94:a9:90:57:ab:80` discovered 20 APs, displayed the strongest
  16, completed secured onboarding, and returned to `WIFI_OFF`; the operator
  also confirmed Portal-mode rescanning. Retained-link release, cancellation,
  failure recovery, and repeated heap/radio cycles remain hardware gates.

## ADR-048: Signed releases update fixed recovery before normal main installation

- Status: Accepted software tranche; interrupted-write and live OTA acceptance
  remain open.
- Compatibility: Keep manifest schema 1 and its signed recovery sequence, size,
  hash, and payload URL fields. Recovery verifies and installs main but never
  writes itself; current main owns factory recovery replacement.
- Ordering: After install consent, current main persists the exact request,
  explicitly selects its own valid `ota_0`, and restarts. Before normal
  services initialize, that main boot brings up only display, touch, LVGL, and
  a bounded progress view; it writes and validates the release-matched factory
  recovery and only then selects it. That updated recovery installs main. A
  newly installed main still pending its health gate must skip this early path;
  the healthy new main clears the completed journal. Factory Reset retains a
  post-main recovery refresh because it originates inside recovery.
- Failure boundary: Before factory erasure, failures retry from the intact
  journal with 1/6/24-hour backoff. After erasure begins, power loss can leave
  recovery invalid. Main remains selected when possible, but loss of both usable
  applications requires the NVS-preserving USB web flash flow. This risk is
  accepted instead of reserving a guardian or second recovery slot. A partial
  recovery image is never deliberately selected. Installed main and recovery
  sequences remain independent for replay protection.
- UX: Confirmation immediately restarts main without painting an intermediate
  normal-runtime progress overlay. The quiet main boot owns the full circular
  **Preparing update** view, updates only bounded status/progress widgets, and
  asks the operator to keep USB power connected. Manual Recovery mode uses a
  two-second hold. A network or
  verification failure boots the normal UI with an explicit **Retry update**
  action; recovery remains unselected.
- Gate: Packaging signatures/hashes, native tests, simulators, and both target
  builds are software evidence. A real old-recovery-to-new-main-to-new-recovery
  cycle plus power loss during the factory write remain hardware acceptance.

## ADR-049: Insta360 GPS and Mini Remote modes are distinct catalog drivers over one runtime

- Status: Accepted implementation; X6 Mini power is panel-confirmed, while
  Start/Stop, reported status, and coexistence validation remain open.
- Catalog identity: Preserve `DriverId::Insta360 = 11` and stable ID
  `insta360.gps_remote` for existing records. Add `DriverId::Insta360Mini = 15`
  with stable ID `insta360.mini_remote`. The Cameras picker exposes **Insta360
  GPS Remote** and **Insta360 Mini Remote** separately because compatible
  models select different remote modes in the camera UI.
- Shared runtime: Both logical drivers use one lazy Insta360 session runtime,
  one `0xCE80`/HID GATT server, and the same bounded callback queue. The Mini
  adapter owns no session array or protocol buffer. GPS and Mini sessions keep
  their selected profile in per-instance state. If both profiles need a
  disconnected pairing identity, the one Insta360 advertiser alternates them
  in 12-second windows; established links remain connected.
- Wire split: GPS advertises `Insta360 Remote (Bleep)` with the captured GPS
  scan response and sends shutter toggle `... 01 02 00`. Mini advertises the
  captured `Insta360 Mini Remote` primary packet plus HID scan response and
  sends shutter toggle `... 01 00 00`. Both consume the shared conservative
  camera-state reducer: GPS `0x10 0x80` display frames and Mini `0x55` phase
  frames.
- Power: Both profiles expose the shared captured shutdown notification
  `... 01 00 03` and serial-addressed ORBIT wake advertisement. X5 supplies
  packet-capture and physical evidence for that path. The operator also
  confirmed that the physical Mini Remote powered the X6 off and on. The
  patched Ble(e)p Mini path subsequently completed physical X6 shutdown,
  correct `CAMERA OFF` transition, and ORBIT wake/reconnect.
- Compatibility: The mode lists photographed from the supplied third-party
  controller manual are candidate-routing evidence, not model verification.
  X6 Mini routing is additionally supported by the live X6 capture. Existing
  per-model support labels do not change until the corresponding panel checks
  pass.
- Diagnostic deviation: A bounded X6 experiment may temporarily replace only
  the Mini complete-name field to test custom-name acceptance. Prefix-free
  `Ble(e)p Remote` and prefix-preserving `Insta360 Bleep Remote` were both not
  shown by the X6. Appearance, HID scan response, GATT, commands, and state were
  unchanged, so Mini mode must use the captured exact `Insta360 Mini Remote`
  identity. Restoring that identity restored X6 discovery and connection.
  Treat exact-name matching as X6-scoped evidence rather than a claim about
  every Insta360 camera model.

## Open decisions

These remain unresolved until their roadmap spikes complete:

- whether hardware evidence justifies reliable Aputure Light state readback or native groups;
- execution-journal persistence and power-loss recovery policy;
- remaining Tascam Portacapture X8 battery/media fields and the exact Deity PR4
  protocol;
- measured memory budgets for minimal and full firmware profiles.
