nethunter/bleep/docs/device-support.md

# Device Support

Status values:

- `Current`: implemented in this repository;
- `Planned`: requirements are defined but implementation has not started;
- `Research`: protocol or stack feasibility must be established;
- `Later`: architecture must allow it, but it is outside the first release.

All current GATT devices use the ADR-021 shared BLE central. They share one
active scanner and bounded asynchronous connection slots while retaining the
matching, pairing, GATT setup, and protocol rules documented below. This is
compile- and host-test-verified. Physical connection and protocol readiness are
tracked separately; Shark, Canon Trigger, Canon Smart, and Tascam publish ready
only after their required setup succeeds. Controller-level connection/security
procedures are queued one at a time, while established links may initialize as
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
