nethunter/bleep/website/assets/hero-product-2x.webp

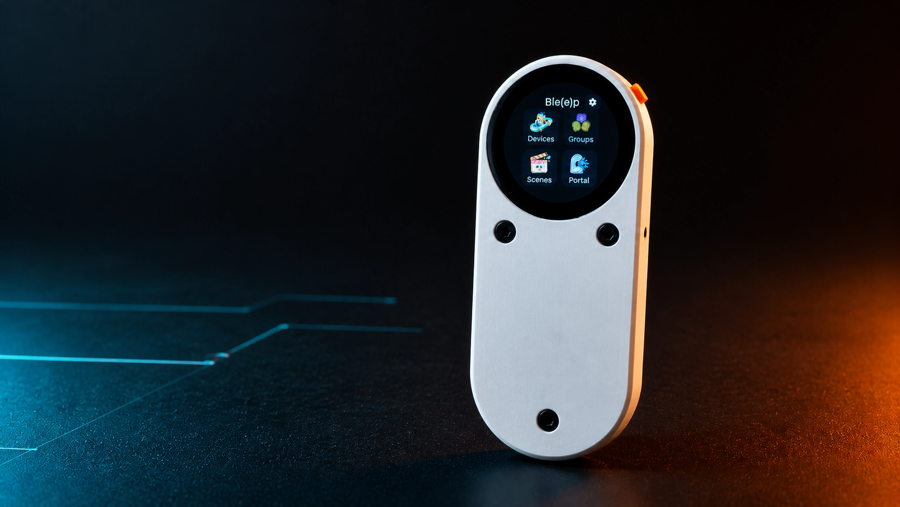
website/assets/hero-product-2x.webp
