nethunter/bleep/website/assets/screens/audio-ready.png

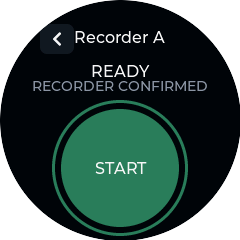
website/assets/screens/audio-ready.png
