nethunter/bleep/website/assets/screens/camera-recording.png

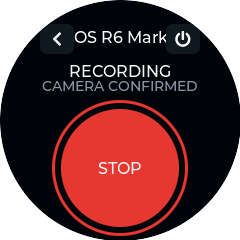
website/assets/screens/camera-recording.png
