nethunter/bleep/website/assets/screens/light-cct.png

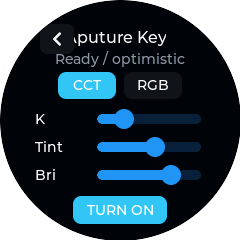
website/assets/screens/light-cct.png
