nethunter/bleep/website/assets/screens/motion-keypoints.png

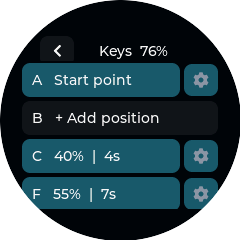
website/assets/screens/motion-keypoints.png
