nethunter/bleep/website/assets/screens/motion-run.png

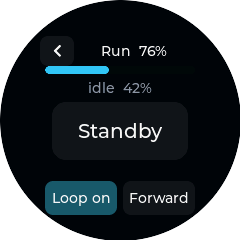
website/assets/screens/motion-run.png
