nethunter/bleep/website/assets/screens/sequence-ready.png

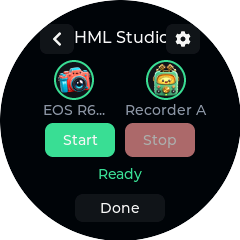
website/assets/screens/sequence-ready.png
