nethunter/bleep/src/firmware_update.cpp

#include "firmware_update.h"

#include <algorithm>
#include <cstdio>
#include <cstring>
#include <memory>
#include <new>

#include "core/firmware_update_policy.h"
#include "core/home_assistant_config.h"
#include "core/panel_settings.h"
#include "core/recovery_install_policy.h"
#ifndef UI_SIMULATOR
#include "core/preferences_store.h"
#endif

#ifdef UI_SIMULATOR

namespace firmware_update {
namespace {
studio::FirmwareUpdatePolicy policy;
Snapshot snapshot;
bool runtimeIdle = true;
bool automaticEligible = true;
bool recoveryRequested = false;
bool factoryResetRequested = false;
}

void FirmwareUpdateService::begin() {
  policy.begin(0);
  snapshot = {};
  recoveryRequested = false;
}
void FirmwareUpdateService::runEarlyRecoveryUpdate(EarlyRecoveryStatusCallback) {}
void FirmwareUpdateService::loop() {}
void FirmwareUpdateService::noteUserActivity() {}
void FirmwareUpdateService::setRuntimeIdle(bool idle, bool eligible) {
  runtimeIdle = idle;
  automaticEligible = eligible;
}
void FirmwareUpdateService::checkNow(bool allowDisconnect) {
  if (!runtimeIdle && !allowDisconnect) {
    snapshot.status = Status::Deferred;
    snapshot.disconnectRequired = true;
    std::strncpy(snapshot.message, "Disconnect devices to check",
                 sizeof(snapshot.message) - 1);
    return;
  }
  snapshot.status = Status::Idle;
  snapshot.disconnectRequired = false;
  snapshot.wifiConfigured = true;
  std::strncpy(snapshot.message, "No update available",
               sizeof(snapshot.message) - 1);
}
bool FirmwareUpdateService::installAvailable() {
  if (!snapshot.updateAvailable) return false;
  snapshot.status = Status::RebootPending;
  snapshot.updateAvailable = false;
  snapshot.notificationPending = false;
  snapshot.recoveryUpdatePending = true;
  std::strncpy(snapshot.message, "Restarting update service",
               sizeof(snapshot.message) - 1);
  return true;
}
void FirmwareUpdateService::dismissAvailable() {
  if (snapshot.updateAvailable) {
    snapshot.notificationPending = false;
    std::strncpy(snapshot.message, "Update available in Settings",
                 sizeof(snapshot.message) - 1);
  }
}
bool FirmwareUpdateService::enterRecovery() {
  recoveryRequested = snapshot.recoveryAvailable;
  return recoveryRequested;
}
bool FirmwareUpdateService::requestFactoryReset() {
  factoryResetRequested = snapshot.recoveryAvailable;
  return factoryResetRequested;
}
Snapshot FirmwareUpdateService::status() const { return snapshot; }
void FirmwareUpdateService::simSetAvailable(const char* version,
                                            uint64_t sequence) {
  snapshot.status = Status::Available;
  snapshot.wifiConfigured = true;
  snapshot.updateAvailable = true;
  snapshot.notificationPending = true;
  snapshot.disconnectRequired = false;
  snapshot.releaseSequence = sequence;
  std::strncpy(snapshot.version, version, sizeof(snapshot.version) - 1);
  std::strncpy(snapshot.message, "Update available", sizeof(snapshot.message) - 1);
}
void FirmwareUpdateService::simSetChecking() {
  snapshot.status = Status::Checking;
  snapshot.wifiConfigured = true;
  snapshot.updateAvailable = false;
  snapshot.notificationPending = false;
  snapshot.disconnectRequired = false;
  std::strncpy(snapshot.message, "Checking for updates",
               sizeof(snapshot.message) - 1);
}
void FirmwareUpdateService::simSetFailure(const char* message) {
  snapshot.status = Status::Failed;
  snapshot.wifiConfigured = true;
  snapshot.updateAvailable = false;
  snapshot.notificationPending = false;
  snapshot.disconnectRequired = false;
  std::strncpy(snapshot.lastResult, message, sizeof(snapshot.lastResult) - 1);
  snapshot.lastResult[sizeof(snapshot.lastResult) - 1] = '\0';
  std::strncpy(snapshot.message, message, sizeof(snapshot.message) - 1);
  snapshot.message[sizeof(snapshot.message) - 1] = '\0';
}
void FirmwareUpdateService::simSetWifiConfigured(bool configured) {
  snapshot.wifiConfigured = configured;
  if (!configured) {
    snapshot.status = Status::Failed;
    std::strncpy(snapshot.message, "Configure Wi-Fi first",
                 sizeof(snapshot.message) - 1);
  }
}
void FirmwareUpdateService::simSetRecoveryAvailable(bool available) {
  snapshot.recoveryAvailable = available;
}
void FirmwareUpdateService::simSetRecoveryRefresh(uint8_t progressPercent) {
  snapshot.status = Status::Downloading;
  snapshot.recoveryUpdatePending = true;
  snapshot.progressPercent = progressPercent;
  std::strncpy(snapshot.message, "Updating recovery", sizeof(snapshot.message) - 1);
}
void FirmwareUpdateService::simClearRecoveryRefresh() {
  snapshot.status = Status::Idle;
  snapshot.recoveryUpdatePending = false;
  snapshot.progressPercent = 0;
}
bool FirmwareUpdateService::simRecoveryRequested() const {
  return recoveryRequested;
}
bool FirmwareUpdateService::simFactoryResetRequested() const {
  return factoryResetRequested;
}
void FirmwareUpdateService::simClearFactoryResetRequested() {
  factoryResetRequested = false;
}
FirmwareUpdateService& service() {
  static FirmwareUpdateService instance;
  return instance;
}
}  // namespace firmware_update

#else

#include <Arduino.h>
#include <ArduinoJson.h>
#include <Preferences.h>
#include <WiFi.h>

#include "wifi_station_cache.h"

#if ARDUINO_USB_CDC_ON_BOOT
#define FW_LOG Serial0
#else
#define FW_LOG Serial
#endif
#include <esp_heap_caps.h>
#include <esp_log.h>
#include <esp_tls.h>

#include "core/update_bundle.h"
#include <esp_http_client.h>
#include <esp_image_format.h>
#include <esp_netif.h>
#include <esp_ota_ops.h>
#include <esp_partition.h>
#include <mbedtls/pk.h>
#include <mbedtls/sha256.h>
#include <time.h>

#include "build_info.h"
#include "core/partition_recovery_backend.h"
#include "core/recovery_journal.h"
#include "firmware_update_keys.h"

namespace firmware_update {
namespace {

// Manifest (<= 1536 bytes) plus the base64 signature line of a bundle.
constexpr size_t kManifestCapacity = 1792;
constexpr size_t kSignatureCapacity = 80;
constexpr int kCheckReceiveBufferSize = 4096;
constexpr int kCheckTransmitBufferSize = 2048;
constexpr int kRecoveryHttpBufferSize = 8192;
constexpr size_t kMaximumImageSize = 0x2C0000;
constexpr size_t kMaximumRecoveryImageSize = 0xF0000;
constexpr uint32_t kConnectTimeoutMs = 12000;
constexpr uint32_t kRequestTimeoutMs = 30000;
constexpr uint32_t kRecoveryRequestTimeoutMs = 120000;
constexpr uint32_t kBootValidationMs = 10000;
constexpr uint32_t kWifiShutdownSettleMs = 250;
constexpr uint32_t kWifiShutdownTimeoutMs = 2000;
constexpr uint32_t kMinimumFreeHeap = 48000;
constexpr uint32_t kMinimumLargestBlock = 36000;
constexpr char kStableManifestUrl[] =
    "https://github.com/nethunter/bleep/releases/latest/download/bleep-update.json";
constexpr char kDevelopmentManifestUrl[] =
    "https://github.com/nethunter/bleep/releases/download/latest/bleep-update.json";
// GitHub and its release CDN currently terminate through different public PKI
// chains. Keep the bounded roots together so an ordinary certificate rotation
// cannot strand the updater before it can verify Ble(e)p's own signed manifest.
constexpr char kUpdateTrustRoots[] = R"CERT(-----BEGIN CERTIFICATE-----
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
MrY=
-----END CERTIFICATE-----
-----BEGIN CERTIFICATE-----
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
-----END CERTIFICATE-----
-----BEGIN CERTIFICATE-----
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
-----END CERTIFICATE-----
)CERT";

enum class TransferKind : uint8_t { None, Bundle, Manifest, Signature, RecoveryImage };
enum class ManifestResult : uint8_t { Invalid, Current, Available };
enum class OperationKind : uint8_t { None, Check, RecoveryRefresh };
enum class RecoveryManifestResult : uint8_t { None, Invalid, Current, Pending };

struct PersistedState {
  uint32_t magic = 0x46575550;
  uint16_t version = 3;
  // Bit flags; the field was reserved (zero) in every stored v3 record.
  uint16_t reserved = 0;
  uint64_t installedSequence = 0;
  uint64_t availableSequence = 0;
  uint64_t dismissedSequence = 0;
  uint64_t lastCheckEpoch = 0;
  char lastResult[32] = "Never checked";
};

studio::FirmwareUpdatePolicy policy;
Snapshot snapshot;
// PersistedState::reserved flag: the current release answered 404 for the
// single-file bundle, so skip that probe (one heavy github.com handshake)
// until a newer release shows up.
constexpr uint16_t kFlagBundleUnavailable = 1u << 0;
// The other 15 bits hold a hash of the release sequence the flag refers to,
// so a newer release clears it and gets probed once.
uint16_t releaseSequenceTag(uint64_t sequence) {
  uint32_t hash = 2166136261u;
  for (int i = 0; i < 8; ++i) {
    hash ^= static_cast<uint8_t>(sequence >> (i * 8));
    hash *= 16777619u;
  }
  return static_cast<uint16_t>(((hash >> 16) ^ hash) & 0x7FFFu);
}
bool bundleMissingThisCheck = false;
uint64_t lastManifestSequence = 0;
bool runtimeIdle = false;
bool automaticEligible = false;
bool ownsWifi = false;
bool wifiShutdownPending = false;
bool bootPending = false;
bool timeSyncStarted = false;
uint32_t bootValidationStarted = 0;
uint32_t operationStarted = 0;
uint32_t wifiShutdownStarted = 0;
esp_http_client_handle_t client = nullptr;
TransferKind transferKind = TransferKind::None;
OperationKind operationKind = OperationKind::None;
char manifest[kManifestCapacity] = {};
size_t manifestLength = 0;
uint8_t signature[kSignatureCapacity] = {};
size_t signatureLength = 0;
char signatureUrl[256] = {};
char bundleUrl[256] = {};
const char* manifestUrl = kStableManifestUrl;
char payloadUrl[320] = {};
size_t expectedImageSize = 0;
uint8_t expectedSha[32] = {};
char recoveryPayloadUrl[320] = {};
size_t expectedRecoveryImageSize = 0;
uint8_t expectedRecoverySha[32] = {};
uint64_t expectedRecoverySequence = 0;
uint64_t installedRecoverySequence = 0;
bool recoveryRefreshPending = false;
bool earlyRecoveryAttemptFailed = false;
uint8_t recoveryRefreshFailures = 0;
uint32_t recoveryRetryAt = 0;
const esp_partition_t* recoveryWritePartition = nullptr;
bool recoveryOtaActive = false;
size_t recoveryBytesWritten = 0;
mbedtls_sha256_context recoveryShaContext;
bool recoveryShaActive = false;
PersistedState persisted;

void setMessage(Status status, const char* message) {
  snapshot.status = status;
  std::strncpy(snapshot.message, message, sizeof(snapshot.message) - 1);
  snapshot.message[sizeof(snapshot.message) - 1] = '\0';
}

bool wifiConfigured(studio::HomeAssistantConfig* output = nullptr) {
  studio::PreferencesHomeAssistantBackend backend;
  studio::HomeAssistantConfigStore store(backend);
  studio::HomeAssistantConfig config;
  const studio::ConfigLoadStatus status = store.load(config);
  const bool configured = status != studio::ConfigLoadStatus::Corrupt &&
                          config.wifiConfigured && config.wifiSsid[0] != '\0';
  snapshot.wifiConfigured = configured;
  if (configured && output != nullptr) *output = config;
  return configured;
}

void savePersisted() {
  Preferences preferences;
  if (!preferences.begin("studio", false)) return;
  preferences.putBytes("fw_update", &persisted, sizeof(persisted));
  preferences.putULong64("fw_rec_seq", installedRecoverySequence);
  preferences.end();
}

void loadPersisted() {
  Preferences preferences;
  if (!preferences.begin("studio", true)) return;
  PersistedState loaded;
  if (preferences.getBytesLength("fw_update") == sizeof(loaded) &&
      preferences.getBytes("fw_update", &loaded, sizeof(loaded)) == sizeof(loaded) &&
      loaded.magic == persisted.magic && loaded.version == persisted.version) {
    persisted = loaded;
    snapshot.lastCheckEpoch = persisted.lastCheckEpoch;
    std::strncpy(snapshot.lastResult, persisted.lastResult,
                 sizeof(snapshot.lastResult) - 1);
  }
  installedRecoverySequence = preferences.getULong64("fw_rec_seq", 0);
  preferences.end();
}

void logHeap(const char* stage);

void recordCheckResult(const char* result) {
  FW_LOG.printf("fw_update event=check_result result=\"%s\"\n", result);
  logHeap("check_result");
  const time_t now = time(nullptr);
  persisted.lastCheckEpoch = now >= 1700000000 ? static_cast<uint64_t>(now) : 0;
  std::strncpy(persisted.lastResult, result, sizeof(persisted.lastResult) - 1);
  persisted.lastResult[sizeof(persisted.lastResult) - 1] = '\0';
  snapshot.lastCheckEpoch = persisted.lastCheckEpoch;
  std::strncpy(snapshot.lastResult, persisted.lastResult,
               sizeof(snapshot.lastResult) - 1);
  snapshot.lastResult[sizeof(snapshot.lastResult) - 1] = '\0';
  savePersisted();
}

void cleanupClient() {
  if (client != nullptr) {
    esp_http_client_cleanup(client);
    client = nullptr;
  }
  transferKind = TransferKind::None;
}

void cleanupRecoveryWrite(bool abortWrite) {
  (void)abortWrite;
  recoveryWritePartition = nullptr;
  recoveryOtaActive = false;
  if (recoveryShaActive) {
    mbedtls_sha256_free(&recoveryShaContext);
    recoveryShaActive = false;
  }
  recoveryBytesWritten = 0;
}

void releaseWifi() {
  cleanupClient();
  if (!ownsWifi) return;
  // disconnect(true) can deinitialize the ESP32-C3 driver before the tcpip
  // task finishes its DHCP release, leaving that task with a dead Wi-Fi queue.
  esp_netif_t* station = esp_netif_get_handle_from_ifkey("WIFI_STA_DEF");
  if (station != nullptr) esp_netif_dhcpc_stop(station);
  WiFi.disconnect(false, false);
  ownsWifi = false;
  wifiShutdownPending = true;
  wifiShutdownStarted = millis();
}

void finishWifiShutdown(uint32_t now) {
  if (!wifiShutdownPending || now - wifiShutdownStarted < kWifiShutdownSettleMs) return;
  if (WiFi.status() == WL_CONNECTED &&
      now - wifiShutdownStarted < kWifiShutdownTimeoutMs) return;
  WiFi.mode(WIFI_OFF);
  wifiShutdownPending = false;
}

void fail(const char* message) {
  const bool checkFailure = true;
  timeSyncStarted = false;
  releaseWifi();
  policy.checked(millis(), false);
  operationKind = OperationKind::None;
  if (checkFailure) recordCheckResult(message);
  setMessage(Status::Failed, message);
}

void scheduleRecoveryRetry(const char* message, bool retryable) {
  const bool recoveryWasBeingWritten = recoveryOtaActive;
  cleanupClient();
  cleanupRecoveryWrite(true);
  if (recoveryWasBeingWritten) snapshot.recoveryAvailable = false;
  releaseWifi();
  operationKind = OperationKind::None;
  if (retryable) {
    static constexpr uint32_t delays[] = {
        60UL * 60UL * 1000UL,
        6UL * 60UL * 60UL * 1000UL,
        24UL * 60UL * 60UL * 1000UL,
    };
    const size_t index = std::min<size_t>(recoveryRefreshFailures,
                                          sizeof(delays) / sizeof(delays[0]) - 1);
    recoveryRetryAt = millis() + delays[index];
    if (recoveryRefreshFailures < 0xff) ++recoveryRefreshFailures;
  } else {
    recoveryRefreshPending = false;
    snapshot.recoveryUpdatePending = false;
  }
  recordCheckResult(message);
  setMessage(Status::Failed, message);
}

void logHeap(const char* stage) {
  FW_LOG.printf("fw_update stage=%s free_heap=%u min_free_heap=%u max_alloc=%u\n",
                stage, static_cast<unsigned>(ESP.getFreeHeap()),
                static_cast<unsigned>(ESP.getMinFreeHeap()),
                static_cast<unsigned>(
                    heap_caps_get_largest_free_block(MALLOC_CAP_8BIT)));
}

esp_err_t onHttpEvent(esp_http_client_event_t* event) {
  if (event->event_id == HTTP_EVENT_ON_CONNECTED) logHeap("tls_connected");
  else if (event->event_id == HTTP_EVENT_ON_FINISH) logHeap("transfer_finished");
  else if (event->event_id == HTTP_EVENT_ERROR) logHeap("transfer_error");
  if (event->event_id != HTTP_EVENT_ON_DATA || event->data_len <= 0) return ESP_OK;
  const uint8_t* bytes = static_cast<const uint8_t*>(event->data);
  const size_t length = static_cast<size_t>(event->data_len);
  if (transferKind == TransferKind::Manifest ||
      transferKind == TransferKind::Bundle) {
    if (manifestLength + length >= sizeof(manifest)) return ESP_FAIL;
    std::memcpy(manifest + manifestLength, bytes, length);
    manifestLength += length;
    manifest[manifestLength] = '\0';
  } else if (transferKind == TransferKind::Signature) {
    if (signatureLength + length > sizeof(signature)) return ESP_FAIL;
    std::memcpy(signature + signatureLength, bytes, length);
    signatureLength += length;
  } else if (transferKind == TransferKind::RecoveryImage) {
    if (!recoveryOtaActive || recoveryBytesWritten + length > expectedRecoveryImageSize ||
        (recoveryBytesWritten == 0 && bytes[0] != 0xE9) ||
        mbedtls_sha256_update_ret(&recoveryShaContext, bytes, length) != 0 ||
        recoveryWritePartition == nullptr ||
        esp_partition_write(recoveryWritePartition, recoveryBytesWritten,
                            bytes, length) != ESP_OK) {
      return ESP_FAIL;
    }
    recoveryBytesWritten += length;
    snapshot.progressPercent = static_cast<uint8_t>(
        std::min<size_t>(99, recoveryBytesWritten * 100 / expectedRecoveryImageSize));
  }
  return ESP_OK;
}

bool startTransfer(const char* url, TransferKind kind) {
  cleanupClient();
  // Parse the trust roots once and share them across the manifest, signature,
  // and redirect handshakes instead of re-parsing the PEM bundle inside each
  // TLS setup; the github.com hops already run within ~1-20 KB of the heap
  // floor on this board.
  static bool globalStoreReady = false;
  if (!globalStoreReady) {
    globalStoreReady = esp_tls_set_global_ca_store(
        reinterpret_cast<const unsigned char*>(kUpdateTrustRoots),
        sizeof(kUpdateTrustRoots)) == ESP_OK;
  }
  esp_http_client_config_t config = {};
  config.url = url;
  if (globalStoreReady) {
    config.use_global_ca_store = true;
  } else {
    config.cert_pem = kUpdateTrustRoots;
  }
  config.user_agent = "Bleep-Firmware-Updater/1";
  config.timeout_ms = 5000;
  config.max_redirection_count = 4;
  config.event_handler = onHttpEvent;
  config.is_async = true;
  // GitHub release responses carry large security headers, and asset redirects
  // use long signed URLs. ESP-IDF configures RX and TX independently; leaving
  // TX at its 512-byte default makes the redirected request line overflow.
  const bool recoveryPayload = kind == TransferKind::RecoveryImage;
  config.buffer_size = recoveryPayload ? kRecoveryHttpBufferSize
                                       : kCheckReceiveBufferSize;
  config.buffer_size_tx = recoveryPayload ? kRecoveryHttpBufferSize
                                          : kCheckTransmitBufferSize;
  transferKind = kind;
  client = esp_http_client_init(&config);
  operationStarted = millis();
  return client != nullptr;
}

bool allowedEffectiveUrl(const char* url) {
  static const char* const prefixes[] = {
      "https://github.com/nethunter/bleep/releases/",
      "https://release-assets.githubusercontent.com/",
      "https://objects.githubusercontent.com/",
      "https://github-releases.githubusercontent.com/",
  };
  for (const char* prefix : prefixes) {
    if (std::strncmp(url, prefix, std::strlen(prefix)) == 0) return true;
  }
  return false;
}

bool hexNibble(char value, uint8_t& result) {
  if (value >= '0' && value <= '9') result = value - '0';
  else if (value >= 'a' && value <= 'f') result = value - 'a' + 10;
  else if (value >= 'A' && value <= 'F') result = value - 'A' + 10;
  else return false;
  return true;
}

bool decodeSha(const char* text, uint8_t output[32]) {
  if (text == nullptr || std::strlen(text) != 64) return false;
  for (size_t i = 0; i < 32; ++i) {
    uint8_t high = 0;
    uint8_t low = 0;
    if (!hexNibble(text[i * 2], high) || !hexNibble(text[i * 2 + 1], low)) return false;
    output[i] = static_cast<uint8_t>((high << 4) | low);
  }
  return true;
}

bool verifyManifest(const char* publicKey) {
  uint8_t digest[32];
  mbedtls_sha256_ret(reinterpret_cast<const unsigned char*>(manifest),
                     manifestLength, digest, 0);
  mbedtls_pk_context key;
  mbedtls_pk_init(&key);
  const int parsed = mbedtls_pk_parse_public_key(
      &key, reinterpret_cast<const unsigned char*>(publicKey),
      std::strlen(publicKey) + 1);
  const int verified = parsed == 0
      ? mbedtls_pk_verify(&key, MBEDTLS_MD_SHA256, digest, sizeof(digest),
                          signature, signatureLength)
      : parsed;
  mbedtls_pk_free(&key);
  return verified == 0;
}

const char* channelName(uint8_t channel) {
  return channel == static_cast<uint8_t>(studio::FirmwareUpdateChannel::Development)
      ? "development" : "stable";
}

const char* channelKeyId(uint8_t channel) {
  return channel == static_cast<uint8_t>(studio::FirmwareUpdateChannel::Development)
      ? firmware_update_keys::kDevelopmentKeyId : firmware_update_keys::kStableKeyId;
}

const char* channelPublicKey(uint8_t channel) {
  return channel == static_cast<uint8_t>(studio::FirmwareUpdateChannel::Development)
      ? firmware_update_keys::kDevelopmentPublicKey
      : firmware_update_keys::kStablePublicKey;
}

RecoveryManifestResult parseRecoveryManifest(
    const studio::RecoveryRecord& record) {
  if (record.manifestLength == 0 || record.manifestLength >= sizeof(manifest) ||
      record.signatureLength == 0 || record.signatureLength > sizeof(signature) ||
      record.channel > static_cast<uint8_t>(studio::FirmwareUpdateChannel::Development)) {
    return RecoveryManifestResult::None;
  }
  std::memcpy(manifest, record.manifest, record.manifestLength);
  manifestLength = record.manifestLength;
  manifest[manifestLength] = '\0';
  std::memcpy(signature, record.signature, record.signatureLength);
  signatureLength = record.signatureLength;
  if (!verifyManifest(channelPublicKey(record.channel))) {
    return RecoveryManifestResult::Invalid;
  }
  JsonDocument document;
  if (deserializeJson(document, manifest, manifestLength) != DeserializationError::Ok) {
    return RecoveryManifestResult::Invalid;
  }
  if (std::strcmp(document["channel"] | "", channelName(record.channel)) != 0 ||
      std::strcmp(document["key_id"] | "", channelKeyId(record.channel)) != 0 ||
      std::strcmp(document["hardware"] | "", build_info::kHardware) != 0 ||
      std::strcmp(document["profile"] | "", "bleep") != 0 ||
      (document["schema"] | 0) != 1 ||
      (document["partition_schema"] | 0) != 2 ||
      (document["recovery_schema"] | 0) != 1 ||
      (document["release_sequence"] | 0ULL) != record.releaseSequence) {
    return RecoveryManifestResult::Invalid;
  }
  if (!document["recovery_sequence"].is<uint64_t>()) {
    return RecoveryManifestResult::None;
  }
  const uint64_t sequence = document["recovery_sequence"] | 0ULL;
  const size_t imageSize = document["recovery_image_size"] | 0U;
  const char* url = document["recovery_payload_url"] | "";
  if (sequence == 0 || imageSize == 0 || imageSize > kMaximumRecoveryImageSize ||
      std::strncmp(url, "https://github.com/nethunter/bleep/releases/download/",
                   std::strlen("https://github.com/nethunter/bleep/releases/download/")) != 0 ||
      !decodeSha(document["recovery_sha256"] | "", expectedRecoverySha)) {
    return RecoveryManifestResult::Invalid;
  }
  if (sequence <= installedRecoverySequence) return RecoveryManifestResult::Current;
  expectedRecoverySequence = sequence;
  expectedRecoveryImageSize = imageSize;
  std::strncpy(recoveryPayloadUrl, url, sizeof(recoveryPayloadUrl) - 1);
  recoveryPayloadUrl[sizeof(recoveryPayloadUrl) - 1] = '\0';
  return RecoveryManifestResult::Pending;
}

ManifestResult parseVerifiedManifest() {
  const bool development = studio::panelSettings().get().firmwareUpdateChannel ==
                           studio::FirmwareUpdateChannel::Development;
  const char* expectedChannel = development ? "development" : "stable";
  const char* expectedKeyId = development ? firmware_update_keys::kDevelopmentKeyId
                                          : firmware_update_keys::kStableKeyId;
  const char* publicKey = development ? firmware_update_keys::kDevelopmentPublicKey
                                      : firmware_update_keys::kStablePublicKey;
  if (!verifyManifest(publicKey)) return ManifestResult::Invalid;
  JsonDocument document;
  if (deserializeJson(document, manifest, manifestLength) != DeserializationError::Ok) {
    return ManifestResult::Invalid;
  }
  if (std::strcmp(document["channel"] | "", expectedChannel) != 0 ||
      std::strcmp(document["key_id"] | "", expectedKeyId) != 0) {
    return ManifestResult::Invalid;
  }
  if ((document["schema"] | 0) != 1 ||
      std::strcmp(document["hardware"] | "", build_info::kHardware) != 0 ||
      std::strcmp(document["profile"] | "", "bleep") != 0 ||
      (document["partition_schema"] | 0) != 2 ||
      (document["recovery_schema"] | 0) != 1) return ManifestResult::Invalid;
  const uint64_t sequence = document["release_sequence"] | 0ULL;
  lastManifestSequence = sequence;
  const size_t imageSize = document["image_size"] | 0U;
  const char* url = document["payload_url"] | "";
  if (imageSize == 0 ||
      imageSize > kMaximumImageSize ||
      std::strncmp(url, "https://github.com/nethunter/bleep/releases/download/",
                   std::strlen("https://github.com/nethunter/bleep/releases/download/")) != 0 ||
      !decodeSha(document["sha256"] | "", expectedSha)) {
    return ManifestResult::Invalid;
  }
  if (sequence <= build_info::kReleaseSequence ||
      sequence <= persisted.installedSequence) return ManifestResult::Current;
  snapshot.releaseSequence = sequence;
  expectedImageSize = imageSize;
  std::strncpy(snapshot.version, document["version"] | "unknown",
               sizeof(snapshot.version) - 1);
  std::strncpy(payloadUrl, url, sizeof(payloadUrl) - 1);
  return ManifestResult::Available;
}

bool beginWifi() {
  studio::HomeAssistantConfig config;
  if (!wifiConfigured(&config)) {
    setMessage(Status::Failed, "Configure Wi-Fi first");
    return false;
  }
  if (WiFi.status() == WL_CONNECTED) {
    ownsWifi = false;
    operationStarted = millis();
    timeSyncStarted = false;
    setMessage(Status::Connecting, "Preparing secure connection");
    return true;
  }
  WiFi.mode(WIFI_STA);
  wifi_station_cache::begin(config.wifiSsid, config.wifiPassword);
  ownsWifi = true;
  operationStarted = millis();
  timeSyncStarted = false;
  setMessage(Status::Connecting, "Connecting to Wi-Fi");
  return true;
}

void startManifestRequest() {
  logHeap("manifest_request");
  const bool development = studio::panelSettings().get().firmwareUpdateChannel ==
                           studio::FirmwareUpdateChannel::Development;
  const char* url = development ? kDevelopmentManifestUrl : kStableManifestUrl;
  manifestLength = 0;
  signatureLength = 0;
  bundleMissingThisCheck = false;
  manifestUrl = url;
  std::snprintf(signatureUrl, sizeof(signatureUrl), "%.*s.sig",
                static_cast<int>(std::strlen(url) - 5), url);
  // Prefer the single-file bundle (manifest + base64 signature): one asset
  // download instead of two halves the TLS handshakes to github.com, which
  // run within a few KB of this board's heap floor. Releases without a bundle
  // answer 404 and the two-file flow takes over.
  std::snprintf(bundleUrl, sizeof(bundleUrl), "%.*s.bundle",
                static_cast<int>(std::strlen(url) - 5), url);
  const bool probeBundle = (persisted.reserved & kFlagBundleUnavailable) == 0;
  if (!startTransfer(probeBundle ? bundleUrl : url,
                     probeBundle ? TransferKind::Bundle
                                 : TransferKind::Manifest)) {
    fail("Could not start update check");
    return;
  }
  setMessage(Status::Checking, "Checking for updates");
}

bool selectRecoveryAndRestart();

bool restartMainForRecoveryUpdate() {
  const esp_partition_t* running = esp_ota_get_running_partition();
  if (running == nullptr || running->subtype != ESP_PARTITION_SUBTYPE_APP_OTA_0 ||
      esp_ota_set_boot_partition(running) != ESP_OK) {
    return false;
  }
  cleanupClient();
  ESP.restart();
  return true;
}

bool startRecoveryRequest() {
  const esp_partition_t* recovery = esp_partition_find_first(
      ESP_PARTITION_TYPE_APP, ESP_PARTITION_SUBTYPE_APP_FACTORY, "recovery");
  if (recovery == nullptr || recovery == esp_ota_get_running_partition() ||
      expectedRecoveryImageSize == 0 ||
      expectedRecoveryImageSize > recovery->size) return false;
  cleanupRecoveryWrite(true);
  if (!startTransfer(recoveryPayloadUrl, TransferKind::RecoveryImage)) return false;
  constexpr size_t kFlashSectorSize = 4096;
  const size_t eraseSize = (expectedRecoveryImageSize + kFlashSectorSize - 1) &
                           ~(kFlashSectorSize - 1);
  if (eraseSize > recovery->size ||
      esp_partition_erase_range(recovery, 0, eraseSize) != ESP_OK) {
    cleanupClient();
    return false;
  }
  recoveryWritePartition = recovery;
  recoveryOtaActive = true;
  mbedtls_sha256_init(&recoveryShaContext);
  recoveryShaActive = true;
  if (mbedtls_sha256_starts_ret(&recoveryShaContext, 0) != 0) {
    cleanupClient();
    cleanupRecoveryWrite(true);
    return false;
  }
  recoveryBytesWritten = 0;
  snapshot.progressPercent = 0;
  setMessage(Status::Downloading, "Updating recovery");
  return true;
}

void finishRecoveryRequest() {
  uint8_t digest[32] = {};
  if (!recoveryOtaActive || recoveryBytesWritten != expectedRecoveryImageSize ||
      !recoveryShaActive ||
      mbedtls_sha256_finish_ret(&recoveryShaContext, digest) != 0 ||
      std::memcmp(digest, expectedRecoverySha, sizeof(digest)) != 0) {
    scheduleRecoveryRetry("Recovery image verification failed", false);
    return;
  }
  mbedtls_sha256_free(&recoveryShaContext);
  recoveryShaActive = false;
  const esp_partition_t* recovery = recoveryWritePartition;
  recoveryWritePartition = nullptr;
  recoveryOtaActive = false;
  esp_image_metadata_t metadata = {};
  const esp_partition_pos_t position = {
      recovery == nullptr ? 0U : recovery->address,
      recovery == nullptr ? 0U : recovery->size,
  };
  if (recovery == nullptr ||
      esp_image_verify(ESP_IMAGE_VERIFY, &position, &metadata) != ESP_OK) {
    recoveryBytesWritten = 0;
    snapshot.recoveryAvailable = false;
    scheduleRecoveryRetry("Recovery image was not bootable", false);
    return;
  }
  recoveryBytesWritten = 0;
  esp_app_desc_t description = {};
  if (esp_ota_get_partition_description(recovery, &description) != ESP_OK) {
    snapshot.recoveryAvailable = false;
    scheduleRecoveryRetry("Recovery validation failed", false);
    return;
  }
  installedRecoverySequence = expectedRecoverySequence;
  snapshot.recoveryAvailable = true;
  savePersisted();
  studio::PartitionRecoveryJournalBackend backend;
  studio::RecoveryJournal journal(backend);
  studio::RecoveryRecord record;
  const bool recordLoaded = journal.load(record);
  const studio::RecoveryInstallStep nextStep = recordLoaded
      ? studio::recoveryInstallStep(
            record.operation, record.releaseSequence,
            build_info::kReleaseSequence, true, true)
      : studio::RecoveryInstallStep::Finish;
  recoveryRefreshPending = false;
  snapshot.recoveryUpdatePending = false;
  recoveryRefreshFailures = 0;
  operationKind = OperationKind::None;
  snapshot.progressPercent = 100;
  if (nextStep == studio::RecoveryInstallStep::BootRecovery) {
    FW_LOG.printf("FW_UPDATE: recovery verified sequence=%llu; booting recovery\n",
                  static_cast<unsigned long long>(installedRecoverySequence));
    recordCheckResult("Recovery updated; firmware pending");
    setMessage(Status::RebootPending, "Starting updated recovery");
    if (selectRecoveryAndRestart()) return;
    releaseWifi();
    setMessage(Status::Failed, "Recovery handoff failed");
    return;
  }
  journal.clear();
  recordCheckResult("Recovery updated");
  releaseWifi();
  setMessage(Status::Idle, "Recovery updated");
}

void prepareRecoveryRefresh() {
  studio::PartitionRecoveryJournalBackend backend;
  studio::RecoveryJournal journal(backend);
  std::unique_ptr<studio::RecoveryRecord> record(
      new (std::nothrow) studio::RecoveryRecord());
  if (!record || !journal.load(*record)) return;
  if (record->operation != studio::RecoveryOperation::InstallRequested &&
      record->operation != studio::RecoveryOperation::ResetComplete) return;
  const RecoveryManifestResult result = parseRecoveryManifest(*record);
  const studio::RecoveryInstallStep nextStep = studio::recoveryInstallStep(
      record->operation, record->releaseSequence, build_info::kReleaseSequence,
      result != RecoveryManifestResult::Invalid &&
          result != RecoveryManifestResult::None,
      result == RecoveryManifestResult::Current);
  if (nextStep == studio::RecoveryInstallStep::WriteRecovery) {
    recoveryRefreshPending = true;
    recoveryRetryAt = millis();
    snapshot.recoveryUpdatePending = true;
    setMessage(Status::Deferred,
               record->operation == studio::RecoveryOperation::InstallRequested &&
                       record->releaseSequence > build_info::kReleaseSequence
                   ? "Preparing updated recovery"
                   : "Finishing recovery update");
    return;
  }
  if (nextStep == studio::RecoveryInstallStep::BootRecovery) {
    snapshot.updateAvailable = false;
    snapshot.notificationPending = false;
    setMessage(Status::RebootPending, "Starting recovery");
    if (!selectRecoveryAndRestart()) {
      setMessage(Status::Failed, "Recovery handoff failed");
    }
    return;
  }
  journal.clear();
  snapshot.recoveryUpdatePending = false;
  if (result == RecoveryManifestResult::Invalid) {
    recordCheckResult("Recovery metadata invalid");
    setMessage(Status::Failed, "Recovery metadata invalid");
  }
}

void finishCheck() {
  snapshot.updateAvailable = true;
  persisted.availableSequence = snapshot.releaseSequence;
  recordCheckResult("Update available");
  snapshot.notificationPending =
      snapshot.releaseSequence != persisted.dismissedSequence;
  snapshot.disconnectRequired = false;
  policy.checked(millis(), true);
  releaseWifi();
  operationKind = OperationKind::None;
  setMessage(Status::Available, "Update available");
}

void handleCompletedTransfer() {
  const int code = esp_http_client_get_status_code(client);
  const TransferKind finished = transferKind;
  char effectiveUrl[384] = {};
  const bool allowed = esp_http_client_get_url(
      client, effectiveUrl, sizeof(effectiveUrl)) == ESP_OK &&
      allowedEffectiveUrl(effectiveUrl);
  cleanupClient();
  if (!allowed) {
    if (finished == TransferKind::RecoveryImage) {
      scheduleRecoveryRetry("Recovery redirect was not allowed", false);
    } else {
      fail("Update redirect was not allowed");
    }
    return;
  }
  if (code == 404 && finished == TransferKind::Bundle) {
    FW_LOG.println("fw_update event=bundle_missing fallback=two_file");
    bundleMissingThisCheck = true;
    manifestLength = 0;
    if (!startTransfer(manifestUrl, TransferKind::Manifest)) {
      fail("Could not start update check");
    }
    return;
  }
  if (code != 200) {
    if (finished == TransferKind::RecoveryImage) {
      scheduleRecoveryRetry(code == 404 ? "Recovery image was not published"
                                         : "Recovery server error", true);
    } else if (code == 404) {
      fail("No signed release published");
    } else {
      fail("Update server error");
    }
    return;
  }
  if (finished == TransferKind::RecoveryImage) {
    finishRecoveryRequest();
  } else if (finished == TransferKind::Manifest) {
    if (!startTransfer(signatureUrl, TransferKind::Signature)) {
      fail("Could not fetch signature");
    }
  } else if (finished == TransferKind::Bundle ||
             finished == TransferKind::Signature) {
    if (finished == TransferKind::Bundle) {
      size_t splitManifestLength = 0;
      if (!studio::splitUpdateBundle(manifest, manifestLength,
                                     splitManifestLength, signature,
                                     sizeof(signature), signatureLength)) {
        fail("Update bundle malformed");
        return;
      }
      manifestLength = splitManifestLength;
      manifest[manifestLength] = '\0';
    }
    const ManifestResult result = parseVerifiedManifest();
    if (result == ManifestResult::Invalid) {
      fail("Update signature or target invalid");
      return;
    }
    if (finished == TransferKind::Signature) {
      const uint16_t tag = releaseSequenceTag(lastManifestSequence);
      if (bundleMissingThisCheck) {
        // Remember which release lacked the bundle; skip the probe for it.
        persisted.reserved = static_cast<uint16_t>(kFlagBundleUnavailable | (tag << 1));
        savePersisted();
      } else if ((persisted.reserved & kFlagBundleUnavailable) != 0 &&
                 static_cast<uint16_t>(persisted.reserved >> 1) != tag) {
        // A different release is published now; it may ship the bundle.
        persisted.reserved = 0;
        savePersisted();
      }
      bundleMissingThisCheck = false;
    }
    if (result == ManifestResult::Current) {
      persisted.availableSequence = 0;
      recordCheckResult("Firmware is up to date");
      policy.checked(millis(), true);
      releaseWifi();
      operationKind = OperationKind::None;
      setMessage(Status::Idle, "Firmware is up to date");
      return;
    }
    finishCheck();
  }
}

bool selectRecoveryAndRestart() {
  const esp_partition_t* recovery = esp_partition_find_first(
      ESP_PARTITION_TYPE_APP, ESP_PARTITION_SUBTYPE_APP_FACTORY, "recovery");
  if (recovery == nullptr || esp_ota_set_boot_partition(recovery) != ESP_OK) return false;
  // The reset itself stops Wi-Fi. Deinitializing it here can race the tcpip
  // task while it is still processing disconnect and DHCP events.
  cleanupClient();
  ownsWifi = false;
  wifiShutdownPending = false;
  ESP.restart();
  return true;
}

bool recoveryPartitionValid() {
  const esp_partition_t* recovery = esp_partition_find_first(
      ESP_PARTITION_TYPE_APP, ESP_PARTITION_SUBTYPE_APP_FACTORY, "recovery");
  esp_app_desc_t description = {};
  return recovery != nullptr &&
         esp_ota_get_partition_description(recovery, &description) == ESP_OK;
}

}  // namespace

void FirmwareUpdateService::begin() {
  const bool preserveEarlyFailure = earlyRecoveryAttemptFailed;
  const Snapshot earlyFailure = snapshot;
  policy.begin(millis());
  snapshot = {};
  operationKind = OperationKind::None;
  recoveryRefreshPending = false;
  recoveryRefreshFailures = 0;
  cleanupRecoveryWrite(true);
  loadPersisted();
  // In async mode every poll without pending bytes logs an EAGAIN "error"
  // from esp_transport; the return codes already carry real failures.
  esp_log_level_set("TRANSPORT_BASE", ESP_LOG_NONE);
  wifiConfigured();
  const esp_partition_t* running = esp_ota_get_running_partition();
  esp_ota_img_states_t state;
  bootPending = running != nullptr &&
                esp_ota_get_state_partition(running, &state) == ESP_OK &&
                state == ESP_OTA_IMG_PENDING_VERIFY;
  bootValidationStarted = millis();
  snapshot.recoveryAvailable = recoveryPartitionValid();
  if (preserveEarlyFailure) {
    snapshot = earlyFailure;
    snapshot.recoveryUpdatePending = true;
    wifiConfigured();
    return;
  }
  if (!bootPending) prepareRecoveryRefresh();
}

void FirmwareUpdateService::runEarlyRecoveryUpdate(
    EarlyRecoveryStatusCallback callback) {
  const esp_partition_t* running = esp_ota_get_running_partition();
  esp_ota_img_states_t imageState = ESP_OTA_IMG_UNDEFINED;
  const bool runningMain = running != nullptr &&
                           running->subtype == ESP_PARTITION_SUBTYPE_APP_OTA_0;
  const bool pendingBootValidation = runningMain &&
      esp_ota_get_state_partition(running, &imageState) == ESP_OK &&
      imageState == ESP_OTA_IMG_PENDING_VERIFY;
  if (!studio::canRunEarlyRecoveryUpdate(runningMain,
                                         pendingBootValidation)) {
    return;
  }

  policy.begin(millis());
  snapshot = {};
  operationKind = OperationKind::None;
  recoveryRefreshPending = false;
  recoveryRefreshFailures = 0;
  cleanupRecoveryWrite(true);
  loadPersisted();
  wifiConfigured();
  snapshot.recoveryAvailable = recoveryPartitionValid();
  runtimeIdle = true;
  automaticEligible = false;
  prepareRecoveryRefresh();
  if (!recoveryRefreshPending) return;

  if (callback != nullptr) callback(snapshot);
  FW_LOG.printf("FW_UPDATE: minimal recovery updater starting; free_heap=%u max_alloc=%u\n",
                static_cast<unsigned>(ESP.getFreeHeap()),
                static_cast<unsigned>(
                    heap_caps_get_largest_free_block(MALLOC_CAP_8BIT)));
  while (recoveryRefreshPending || client != nullptr ||
         operationKind == OperationKind::RecoveryRefresh) {
    loop();
    if (callback != nullptr) callback(snapshot);
    if (snapshot.status == Status::Failed) {
      earlyRecoveryAttemptFailed = true;
      while (wifiShutdownPending && millis() - wifiShutdownStarted <
                 kWifiShutdownTimeoutMs) {
        finishWifiShutdown(millis());
        delay(5);
      }
      FW_LOG.printf("FW_UPDATE: minimal recovery updater failed: %s; free_heap=%u "
                    "min_free_heap=%u\n",
                    snapshot.message,
                    static_cast<unsigned>(ESP.getFreeHeap()),
                    static_cast<unsigned>(ESP.getMinFreeHeap()));
      return;
    }
    delay(5);
  }
}

void FirmwareUpdateService::loop() {
  const uint32_t now = millis();
  finishWifiShutdown(now);
  if (bootPending && now - bootValidationStarted >= kBootValidationMs) {
    if (esp_ota_mark_app_valid_cancel_rollback() == ESP_OK) {
      studio::PartitionRecoveryJournalBackend backend;
      studio::RecoveryJournal journal(backend);
      std::unique_ptr<studio::RecoveryRecord> completed(
          new (std::nothrow) studio::RecoveryRecord());
      if (completed && journal.load(*completed) &&
          completed->releaseSequence > persisted.installedSequence) {
        persisted.installedSequence = completed->releaseSequence;
        savePersisted();
      }
      bootPending = false;
      prepareRecoveryRefresh();
    }
  }
  if (snapshot.status == Status::Connecting) {
    if (operationKind == OperationKind::RecoveryRefresh && !runtimeIdle) {
      scheduleRecoveryRetry("Recovery update deferred", true);
      return;
    }
    if (WiFi.status() == WL_CONNECTED) {
      if (!timeSyncStarted) {
        logHeap("wifi_connected");
        studio::HomeAssistantConfig config;
        if (wifiConfigured(&config)) {
          wifi_station_cache::rememberCurrent(config.wifiSsid);
        }
        configTime(0, 0, "pool.ntp.org", "time.nist.gov");
        timeSyncStarted = true;
        operationStarted = now;
        setMessage(Status::Connecting, "Synchronizing secure time");
        return;
      }
      if (time(nullptr) < 1700000000) {
        if (now - operationStarted >= kConnectTimeoutMs) {
          fail("Secure time unavailable");
        }
        return;
      }
      timeSyncStarted = false;
      if (operationKind == OperationKind::RecoveryRefresh) {
        if (!startRecoveryRequest()) {
          scheduleRecoveryRetry("Could not start recovery update", true);
        }
      } else {
        startManifestRequest();
      }
    } else if (now - operationStarted >= kConnectTimeoutMs) {
      if (operationKind == OperationKind::RecoveryRefresh) {
        scheduleRecoveryRetry("Recovery Wi-Fi timed out", true);
      } else {
        wifi_station_cache::invalidate();
        fail("Wi-Fi connection timed out");
      }
    }
    return;
  }
  if (client != nullptr) {
    if (!runtimeIdle && operationKind != OperationKind::RecoveryRefresh) {
      policy.deferStartup();
      releaseWifi();
      operationKind = OperationKind::None;
      setMessage(Status::Deferred, "Update check deferred");
      return;
    }
    static uint32_t lastHeapSampleMs = 0;
    if (now - lastHeapSampleMs >= 250) {
      lastHeapSampleMs = now;
      logHeap("perform");
    }
    const esp_err_t result = esp_http_client_perform(client);
    if (result == ESP_OK) handleCompletedTransfer();
    else if (result != ESP_ERR_HTTP_EAGAIN && result != ESP_ERR_HTTP_CONNECTING) {
      FW_LOG.printf("[fw-update] transfer failed: %s (0x%x)\n",
                    esp_err_to_name(result), static_cast<unsigned>(result));
      if (operationKind == OperationKind::RecoveryRefresh) {
        scheduleRecoveryRetry("Recovery transfer failed", true);
      } else {
        fail("Network transfer failed");
      }
    } else if (now - operationStarted >=
               (operationKind == OperationKind::RecoveryRefresh
                    ? kRecoveryRequestTimeoutMs : kRequestTimeoutMs)) {
      if (operationKind == OperationKind::RecoveryRefresh) {
        scheduleRecoveryRetry("Recovery request timed out", true);
      } else {
        fail("Update request timed out");
      }
    }
    return;
  }
  const bool heapSafe = ESP.getFreeHeap() >= kMinimumFreeHeap &&
      heap_caps_get_largest_free_block(MALLOC_CAP_8BIT) >= kMinimumLargestBlock;
  if (recoveryRefreshPending) {
    snapshot.recoveryUpdatePending = true;
    if (!earlyRecoveryAttemptFailed && !bootPending && runtimeIdle && heapSafe &&
        static_cast<int32_t>(now - recoveryRetryAt) >= 0) {
      operationKind = OperationKind::RecoveryRefresh;
      if (!beginWifi()) {
        scheduleRecoveryRetry("Recovery Wi-Fi unavailable", true);
      }
    }
    return;
  }
  if (snapshot.status == Status::Available ||
      snapshot.status == Status::RebootPending) return;
  if (!runtimeIdle) policy.deferStartup();
  if (policy.immediateRequested() && runtimeIdle && !heapSafe) {
    setMessage(Status::Deferred, "Waiting for available memory");
  }
  const bool checkEligible = runtimeIdle && heapSafe &&
      (automaticEligible || policy.immediateRequested());
  if (policy.shouldCheck(now, checkEligible, snapshot.wifiConfigured)) {
    operationKind = OperationKind::Check;
    if (!beginWifi()) {
      operationKind = OperationKind::None;
      policy.checked(now, false);
    }
  }
}

void FirmwareUpdateService::noteUserActivity() { policy.noteUserActivity(millis()); }
void FirmwareUpdateService::setRuntimeIdle(bool idle, bool eligible) {
  if (eligible && !automaticEligible) wifiConfigured();
  runtimeIdle = idle;
  automaticEligible = eligible;
}

void FirmwareUpdateService::checkNow(bool allowDisconnect) {
  wifiConfigured();
  if (!snapshot.wifiConfigured) {
    setMessage(Status::Failed, "Configure Wi-Fi first");
    return;
  }
  if (!runtimeIdle && !allowDisconnect) {
    snapshot.disconnectRequired = true;
    setMessage(Status::Deferred, "Disconnect devices to check");
    return;
  }
  if (recoveryRefreshPending || earlyRecoveryAttemptFailed) {
    if (!restartMainForRecoveryUpdate()) {
      setMessage(Status::Failed, "Could not restart update service");
    }
    return;
  }
  snapshot.disconnectRequired = false;
  policy.requestImmediate();
}

bool FirmwareUpdateService::installAvailable() {
  if (!snapshot.updateAvailable || payloadUrl[0] == '\0' ||
      expectedImageSize == 0 || manifestLength == 0 || signatureLength == 0) return false;
  std::unique_ptr<studio::RecoveryRecord> record(
      new (std::nothrow) studio::RecoveryRecord());
  if (!record) return false;
  studio::PartitionRecoveryJournalBackend backend;
  studio::RecoveryJournal journal(backend);
  journal.load(*record);
  record->operation = studio::RecoveryOperation::InstallRequested;
  record->channel = static_cast<uint8_t>(
      studio::panelSettings().get().firmwareUpdateChannel);
  record->releaseSequence = snapshot.releaseSequence;
  record->manifestLength = manifestLength;
  record->signatureLength = signatureLength;
  std::memcpy(record->manifest, manifest, manifestLength);
  std::memcpy(record->signature, signature, signatureLength);
  if (!journal.save(*record)) return false;
  const RecoveryManifestResult result = parseRecoveryManifest(*record);
  const studio::RecoveryInstallStep nextStep = studio::recoveryInstallStep(
      record->operation, record->releaseSequence, build_info::kReleaseSequence,
      result != RecoveryManifestResult::Invalid &&
          result != RecoveryManifestResult::None,
      result == RecoveryManifestResult::Current);
  if (nextStep == studio::RecoveryInstallStep::Reject) {
    setMessage(Status::Failed, "Recovery metadata invalid");
    return false;
  }
  snapshot.updateAvailable = false;
  snapshot.notificationPending = false;
  if (nextStep == studio::RecoveryInstallStep::BootRecovery) {
    setMessage(Status::RebootPending, "Starting recovery");
    if (selectRecoveryAndRestart()) return true;
    setMessage(Status::Failed, "Recovery handoff failed");
    return false;
  }
  if (nextStep != studio::RecoveryInstallStep::WriteRecovery) {
    journal.clear();
    setMessage(Status::Failed, "Update is already installed");
    return false;
  }
  FW_LOG.printf("FW_UPDATE: updating recovery sequence=%llu before main sequence=%llu\n",
                static_cast<unsigned long long>(expectedRecoverySequence),
                static_cast<unsigned long long>(snapshot.releaseSequence));
  snapshot.recoveryUpdatePending = true;
  recoveryRefreshPending = true;
  recoveryRefreshFailures = 0;
  FW_LOG.printf("FW_UPDATE: restarting into minimal updater for recovery sequence=%llu\n",
                static_cast<unsigned long long>(expectedRecoverySequence));
  if (restartMainForRecoveryUpdate()) return true;
  setMessage(Status::Failed, "Could not restart update service");
  return false;
}

void FirmwareUpdateService::dismissAvailable() {
  if (!snapshot.updateAvailable) return;
  persisted.dismissedSequence = snapshot.releaseSequence;
  savePersisted();
  snapshot.notificationPending = false;
  setMessage(Status::Available, "Update available in Settings");
}

bool FirmwareUpdateService::enterRecovery() {
  studio::PartitionRecoveryJournalBackend backend;
  studio::RecoveryJournal journal(backend);
  std::unique_ptr<studio::RecoveryRecord> record(
      new (std::nothrow) studio::RecoveryRecord());
  if (!record) {
    setMessage(Status::Failed, "Not enough memory for recovery");
    return false;
  }
  journal.load(*record);
  *record = {};
  record->operation = studio::RecoveryOperation::RecoveryModeRequested;
  if (!journal.save(*record)) {
    setMessage(Status::Failed, "Could not prepare recovery");
    return false;
  }
  setMessage(Status::RebootPending, "Entering recovery");
  if (selectRecoveryAndRestart()) return true;
  setMessage(Status::Failed, "Recovery handoff failed");
  return false;
}

bool FirmwareUpdateService::requestFactoryReset() {
  std::unique_ptr<studio::RecoveryRecord> record(
      new (std::nothrow) studio::RecoveryRecord());
  if (!record) return false;
  studio::PartitionRecoveryJournalBackend backend;
  studio::RecoveryJournal journal(backend);
  journal.load(*record);
  *record = {};
  record->operation = studio::RecoveryOperation::FactoryResetRequested;
  record->channel = static_cast<uint8_t>(studio::FirmwareUpdateChannel::Stable);
  return journal.save(*record) && selectRecoveryAndRestart();
}

Snapshot FirmwareUpdateService::status() const { return snapshot; }

FirmwareUpdateService& service() {
  static FirmwareUpdateService instance;
  return instance;
}

}  // namespace firmware_update

#endif
